colinbdclark/lichen-eurorack-hardware/lichen-breadboard-adaptors/lichen-breadboard-alpha-pot-dual-adaptor/lichen-breadboard-alpha-pot-dual-adaptor.kicad_pcb

## KiCad design lichen-breadboard-adaptors/lichen-breadboard-alpha-pot-dual-adaptor/lichen-breadboard-alpha-pot-dual-adaptor.kicad_pcb (2025-12-30)

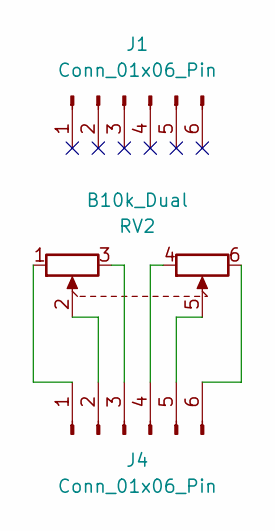
[picture p50: schematic lichen-breadboard-alpha-pot-dual-adaptor.kicad_sch]

Parts:
J1, J4: Conn_01x06_Pin; PinHeader_1x06_P2.54mm_Vertical
RV2: B10k_Dual; Potentiometer_Alpha_RD902F-40-00D_Dual_Vertical; Part Number RD90F-40

Connections:
unnamed: J4.1, RV2.1
unnamed: J4.2, RV2.2
unnamed: J4.3, RV2.3
unnamed: J4.4, RV2.4
unnamed: J4.5, RV2.5
unnamed: J4.6, RV2.6

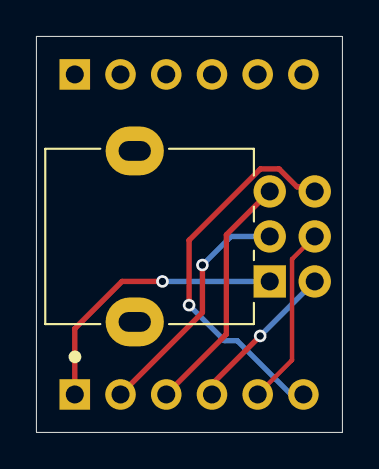
[picture p51: board lichen-breadboard-alpha-pot-dual-adaptor.kicad_pcb from above]

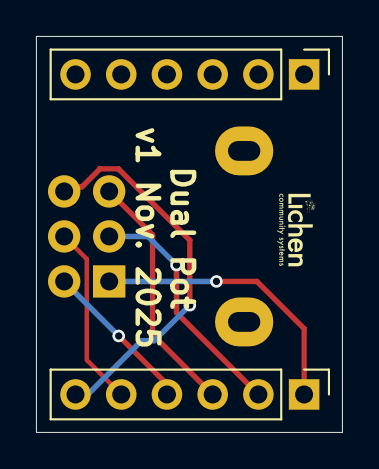
[picture p52: board lichen-breadboard-alpha-pot-dual-adaptor.kicad_pcb from below]

Board: 2 copper layers, 17.0 x 22.0 mm, 3 parts (2 on the bottom side), 6 nets.
