colinbdclark/lichen-eurorack-hardware/lichen-breadboard-adaptors/lichen-breadboard-spdt-switch-adaptor/lichen-breadboard-spdt-switch-adaptor.kicad_pcb

## KiCad design lichen-breadboard-adaptors/lichen-breadboard-spdt-switch-adaptor/lichen-breadboard-spdt-switch-adaptor.kicad_pcb (2025-12-30)

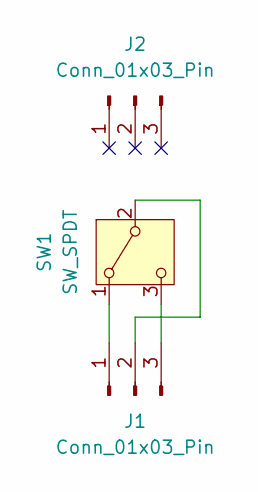
[picture p53: schematic lichen-breadboard-spdt-switch-adaptor.kicad_sch]

Parts:
J1, J2: Conn_01x03_Pin; PinHeader_1x03_P2.54mm_Vertical
SW1: SW_SPDT; Miniature_Switch_SPDT_2.54MM

Connections:
unnamed: J1.1, SW1.1 (A)
unnamed: J1.2, SW1.2 (B)
unnamed: J1.3, SW1.3 (C)

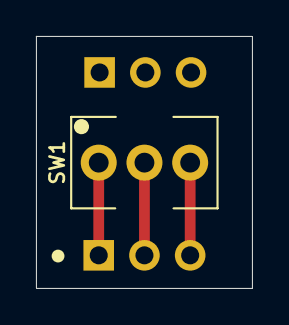
[picture p54: board lichen-breadboard-spdt-switch-adaptor.kicad_pcb from above]

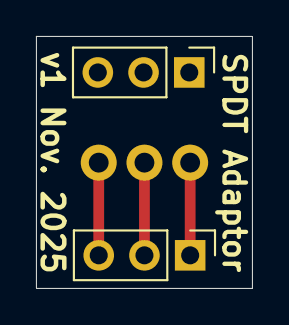
[picture p55: board lichen-breadboard-spdt-switch-adaptor.kicad_pcb from below]

Board: 2 copper layers, 12.0 x 14.0 mm, 3 parts (2 on the bottom side), 3 nets.
