colinbdclark/lichen-eurorack-hardware/lichen-breadboard-adaptors/lichen-breadboard-alpha-pot-single-adaptor/lichen-breadboard-alpha-pot-single-adaptor.kicad_pcb

## KiCad design lichen-breadboard-adaptors/lichen-breadboard-alpha-pot-single-adaptor/lichen-breadboard-alpha-pot-single-adaptor.kicad_pcb (2025-12-30)

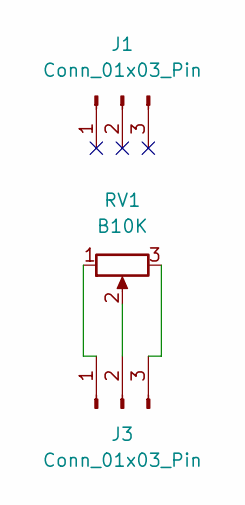
[picture p56: schematic lichen-breadboard-alpha-pot-single-adaptor.kicad_sch]

Parts:
J1, J3: Conn_01x03_Pin; PinHeader_1x03_P2.54mm_Vertical
RV1: B10K; Potentiometer_Alpha_RD901_Eurorack; Part Number RD901F-40

Connections:
unnamed: J3.1, RV1.1
unnamed: J3.2, RV1.2
unnamed: J3.3, RV1.3

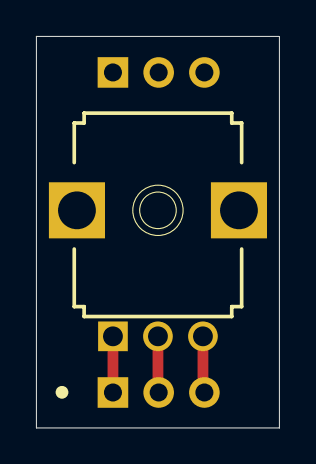
[picture p57: board lichen-breadboard-alpha-pot-single-adaptor.kicad_pcb from above]

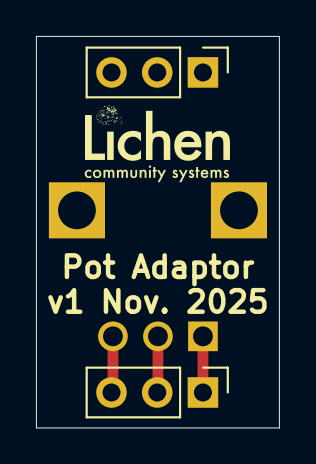
[picture p58: board lichen-breadboard-alpha-pot-single-adaptor.kicad_pcb from below]

Board: 2 copper layers, 13.5 x 21.8 mm, 3 parts (2 on the bottom side), 3 nets.
