colinbdclark/lichen-eurorack-hardware/lichen-four/lichen-four-board/lichen-four-board.kicad_pcb

## KiCad design lichen-four/lichen-four-board/lichen-four-board.kicad_pcb (2025-12-17)

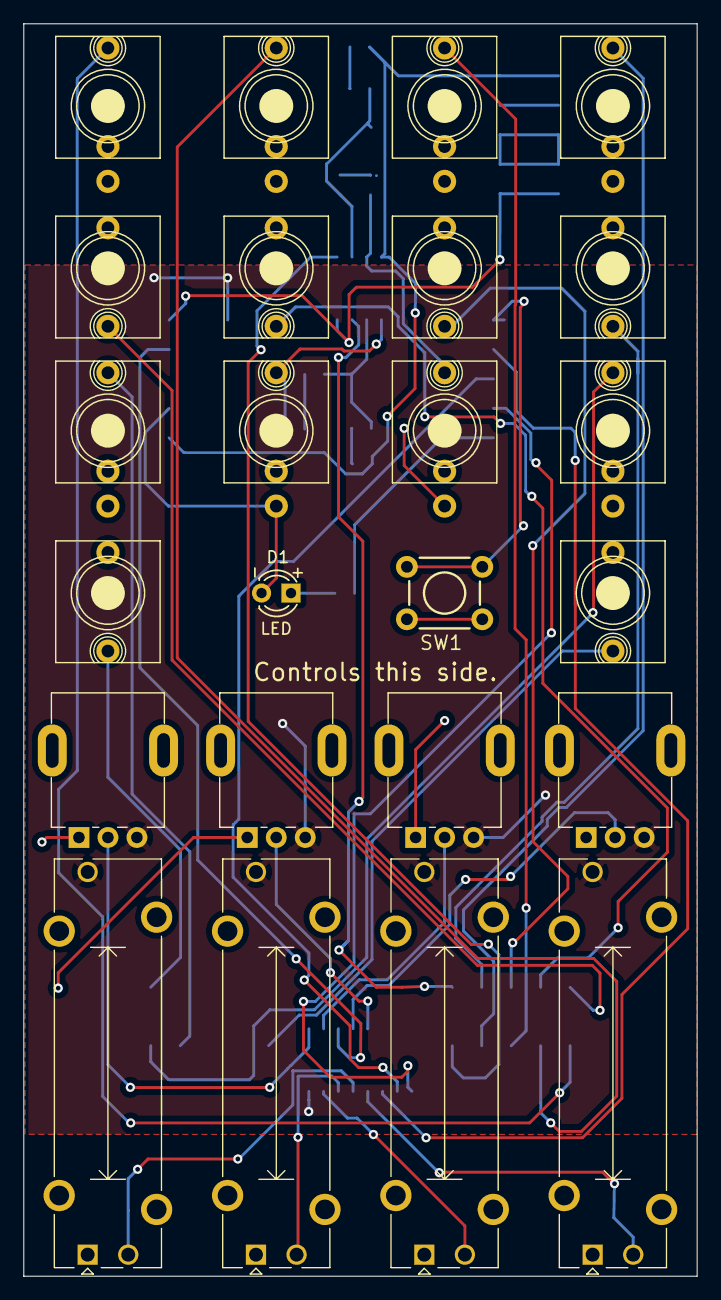
[picture p59: board lichen-four-board.kicad_pcb from above]

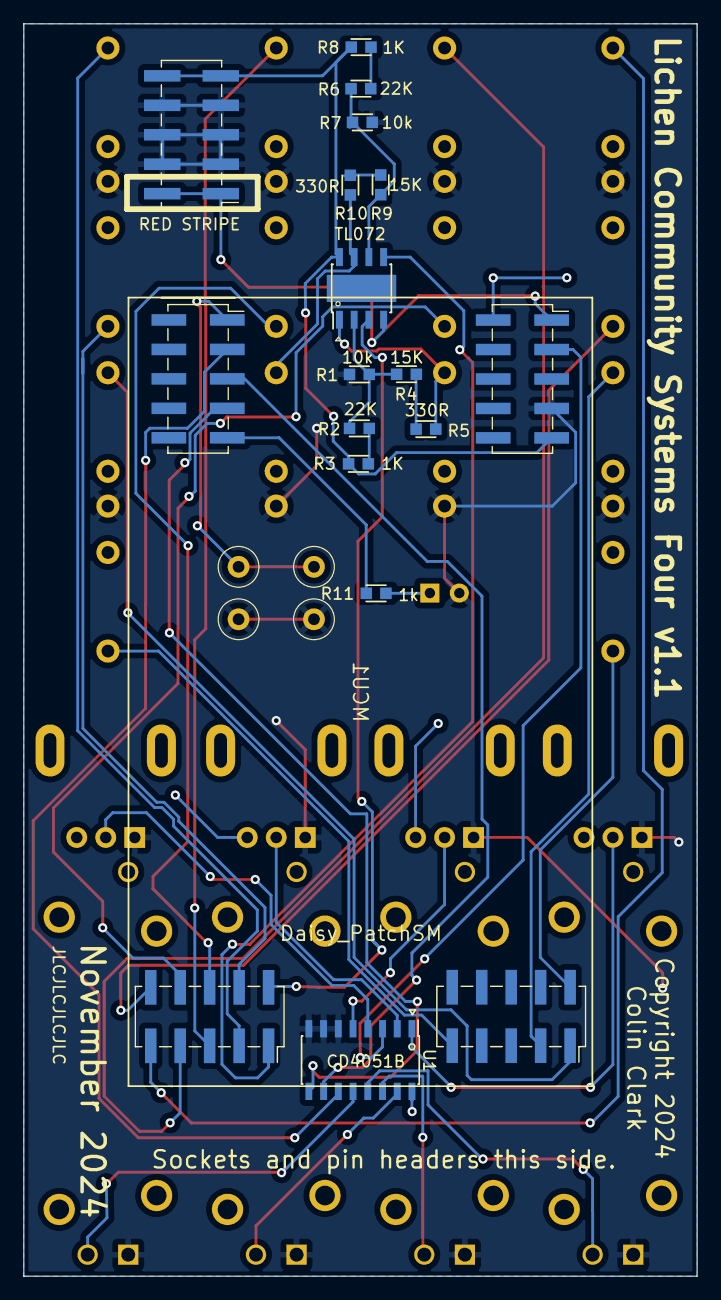
[picture p60: board lichen-four-board.kicad_pcb from below]

Board: 2 copper layers, 58.1 x 108.0 mm, 39 parts (14 on the bottom side), 41 nets.

Parts:
D1: LED; LED_3mm_C1A2_Polarity_Indicator
J1, J2, J3, J4, J9, J10, J11, J12: Eurorack_Mono_Jack; AudioJack_WQP518MA
J5, J6, J7, J8, J13, J14: Eurorack_Mono_Jack; AudioJack_WQP518MA_No_S
MCU1: Daisy_PatchSM; Daisy_Patch_Submodule_SMD
PWR1: Eurorack_Power; PinHeader_2x05_P2.54mm_Vertical_SMD
R1, R6: 10k; R_0603
R2, R7: 22K; R_0603
R3, R8: 1K; R_0603
R4, R9: 15K; R_0603
R5, R10: 330R; R_0603
R11: 1k; R_0603
RV1, RV2, RV3, RV4: R_Potentiometer; Potentiometer_Bourns_PTA2043_Single_Slide
RV5, RV6, RV7, RV8: Eurorack_Pot; Potentiometer_Alpha_R0904N
SW1: TL1105SPF250Q; TL1105SPF250Q_SILK
U1: CD4051B; SOIC-16_3.9x9.9mm_Pitch1.27mm
U2: TL072; SOIC-8-1EP_3.9x4.9mm_Pitch1.27mm_HandSolder

Connections:
+3.3V: MCU1.A10 (+3V3), RV1.3, RV2.3, RV3.3, RV4.3, RV5.3, RV6.3, RV7.3, RV8.3, U1.16 (VDD)
+12V: MCU1.A5 (+12V), PWR1.9 (+12V), PWR1.10 (+12V), R3.2, R8.2, U2.8 (V+)
-12V: MCU1.A1 (-12V), PWR1.1 (-12V), PWR1.2 (-12V), U2.4 (V-)
ADC_MUX: MCU1.A2 (UART_RX), U1.3 (X)
AUDIO_CV_OUT_1: J9.T (Tip), MCU1.B2 (AUDIO_OUT_L)
AUDIO_CV_OUT_2: J12.T (Tip), MCU1.B1 (AUDIO_OUT_R)
BIPOLAR_CV_OUT_1: J10.T (Tip), R5.2, U2.1
BIPOLAR_CV_OUT_2: J11.T (Tip), R10.2, U2.7
CHANNEL_SEL_A: MCU1.D2 (SDMMC_D3), U1.11 (A)
CHANNEL_SEL_B: MCU1.D3 (SDMMC_D2), U1.10 (B)
CHANNEL_SEL_C: MCU1.D4 (SDMMC_D1), U1.9 (C)
CV_JACK_1: J1.T (Tip), MCU1.C5 (CV1)
CV_JACK_2: J2.T (Tip), MCU1.C4 (CV2)
CV_JACK_3: J3.T (Tip), MCU1.C3 (CV3)
CV_JACK_4: J4.T (Tip), MCU1.C2 (CV4)
CV_JACK_5: J5.T (Tip), MCU1.C6 (CV5)
CV_JACK_6: J6.T (Tip), MCU1.C7 (CV6)
CV_JACK_7: J7.T (Tip), MCU1.C8 (CV7)
CV_JACK_8: J8.T (Tip), MCU1.C9 (CV8)
GATE_IN_1: J13.T (Tip), MCU1.B10 (GATE_IN_1)
GATE_OUT_1: J14.T (Tip), MCU1.B5 (GATE_OUT_1)
GND: D1.1 (K), J1.S (Sleeve), J2.S (Sleeve), J3.S (Sleeve), J4.S (Sleeve), J9.S (Sleeve), J10.S (Sleeve), J11.S (Sleeve), J12.S (Sleeve), MCU1.A4 (GND), PWR1.3 (GND), PWR1.4 (GND), PWR1.5 (GND), PWR1.6 (GND), PWR1.7 (GND), PWR1.8 (GND), R1.1, R6.1, RV1.1, RV2.1, RV3.1, RV4.1, RV5.1, RV6.1, RV7.1, RV8.1, SW1.3, SW1.4, U1.6 (INH), U1.7 (VEE), U1.8 (VSS)
GPIO_BUTTON_1: MCU1.D1 (SPI_NSS), SW1.1, SW1.2
GPIO_LED_1: MCU1.D5 (SDMMC_D0), R11.2
unnamed: D1.2 (A), R11.1
unnamed: R2.2, R3.1
unnamed: R4.2, R5.1
unnamed: R7.2, R8.1
unnamed: R9.2, R10.1
unnamed: RV1.2, U1.13 (X0)
unnamed: RV2.2, U1.14 (X1)
unnamed: RV3.2, U1.15 (X2)
unnamed: RV4.2, U1.12 (X3)
unnamed: RV5.2, U1.1 (X4)
unnamed: RV6.2, U1.5 (X5)
unnamed: RV7.2, U1.2 (X6)
unnamed: RV8.2, U1.4 (X7)
unnamed: R1.2, R2.1, R4.1, U2.2 (-)
unnamed: R6.2, R7.1, R9.1, U2.6 (-)
UNIPOLAR_CV_OUT_1: MCU1.C10 (CV_OUT_1), U2.3 (+)
UNIPOLAR_CV_OUT_2: MCU1.C1 (CV_OUT_2), U2.5 (+)
