colinbdclark/lichen-eurorack-hardware/lichen-passive-mutes/lichen-passive-mutes-board/lichen-passive-mutes-board.kicad_pcb

## KiCad design lichen-passive-mutes/lichen-passive-mutes-board/lichen-passive-mutes-board.kicad_pcb (2024-10-25)

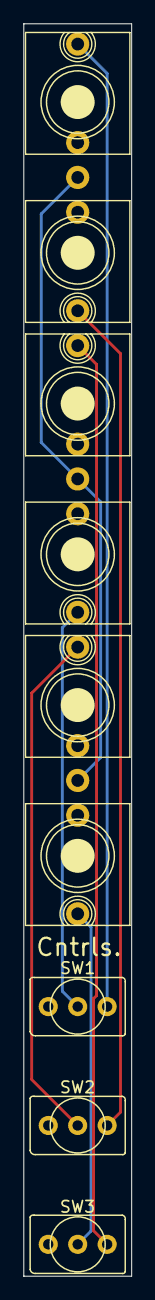
[picture p61: board lichen-passive-mutes-board.kicad_pcb from above]

Board: 2 copper layers, 9.3 x 108.0 mm, 9 parts (0 on the bottom side), 7 nets.

Parts:
J1, J3, J5: Eurorack_Mono_Jack; AudioJack_WQP518MA
J2, J4, J6: Eurorack_Mono_Jack; AudioJack_WQP518MA_No_S
SW1, SW2, SW3: SW_SPDT; Switch_Toggle_SPDT_SubMini

Connections:
GND: J1.S (Sleeve), J3.S (Sleeve), J5.S (Sleeve)
unnamed: J1.T (Tip), SW1.1 (A)
unnamed: J2.T (Tip), SW2.1 (A)
unnamed: J3.T (Tip), SW3.1 (A)
unnamed: J4.T (Tip), SW1.2 (B)
unnamed: J5.T (Tip), SW2.2 (B)
unnamed: J6.T (Tip), SW3.2 (B)
