colinbdclark/lichen-eurorack-hardware/bifocals-filter/lichen-bifocals-control-board/lichen-bifocals-control-board.kicad_pcb

## KiCad design bifocals-filter/lichen-bifocals-control-board/lichen-bifocals-control-board.kicad_pcb (2024-10-25)

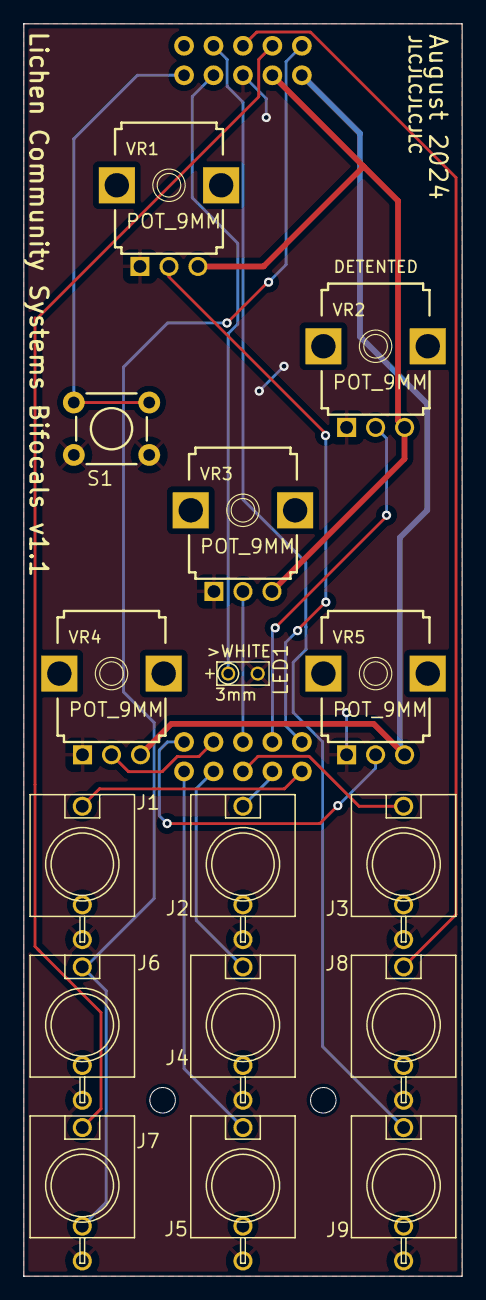
[picture p62: board lichen-bifocals-control-board.kicad_pcb from above]

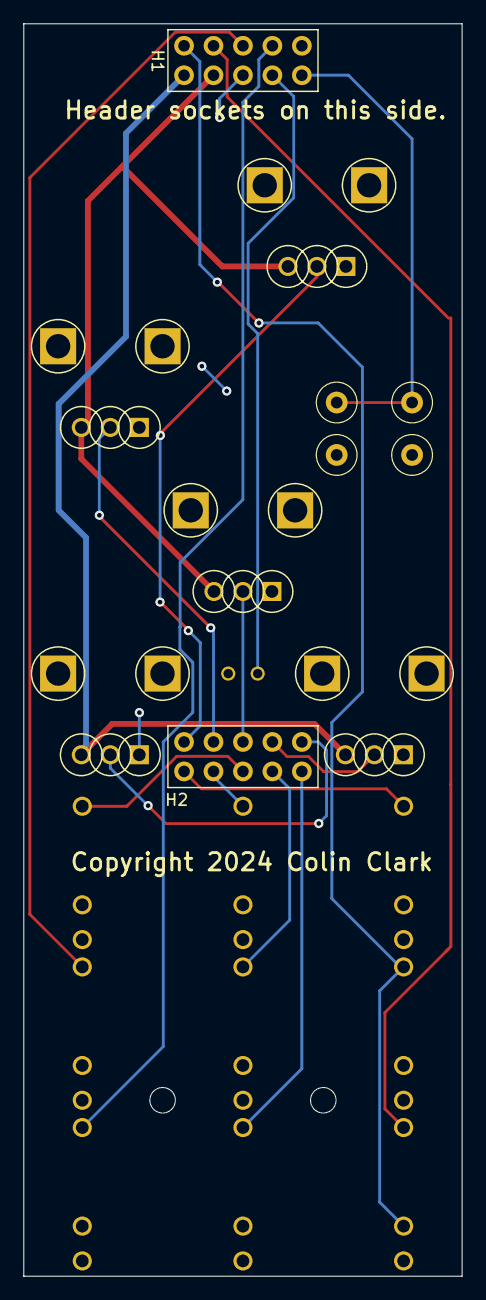
[picture p63: board lichen-bifocals-control-board.kicad_pcb from below]

Board: 2 copper layers, 37.8 x 108.0 mm, 20 parts (2 on the bottom side), 19 nets.

Parts:
H1, H2: PIN_HEADER_2x5; Pins_2x05_2.54mm_TH
J1, J2, J3, J4, J5, J6, J7, J8, J9: EURO_JACK; S_JACK
LED1: LED
MH2, MH2#2: MountingHole_2.2mm_M2
S1: TAC_SWITCH_PTH; TL1105SPF250Q_SILK
VR1, VR2, VR3, VR4, VR5: POT_9MM; 9MM_SNAP-IN_POT_SILK

Connections:
+3.3V: H1.1, VR4.3, VR5.3
+5V: H1.3, VR1.3, VR2.3, VR3.3
AUDIO_IN_L: H1.2, J6.TIP, J7.NORM
AUDIO_IN_R: H1.4, J7.TIP
AUDIO_OUT_L: H1.6, J8.TIP
AUDIO_OUT_R: H1.8, J9.TIP
BUTTON: H1.9, S1.1, S1.2
GND: H1.5, J1.GND, J2.GND, J3.GND, J4.GND, J5.GND, J6.GND, J7.GND, J8.GND, J9.GND, LED1.K (C), S1.3, S1.4, VR1.1, VR2.1, VR3.1, VR4.1, VR5.1
JACK_CV_1: H2.1, J1.TIP
JACK_CV_2: H2.3, J2.TIP
JACK_CV_3: H2.5, J3.TIP
JACK_CV_4: H2.7, J4.TIP
JACK_CV_5: H2.9, J5.TIP
LED_CV_OUT: H1.7, LED1.A
POT_1_CV_6: H2.2, VR1.2
POT_2_CV_7: H2.4, VR2.2
POT_3_CV_8: H2.6, VR3.2
POT_4_CV_9: H2.8, VR4.2
POT_5_CV_10: H2.10, VR5.2
