colinbdclark/lichen-eurorack-hardware/lichen-freddie/lichen-freddie-board/lichen-freddie-board.kicad_pcb

## KiCad design lichen-freddie/lichen-freddie-board/lichen-freddie-board.kicad_pcb (2024-10-25)

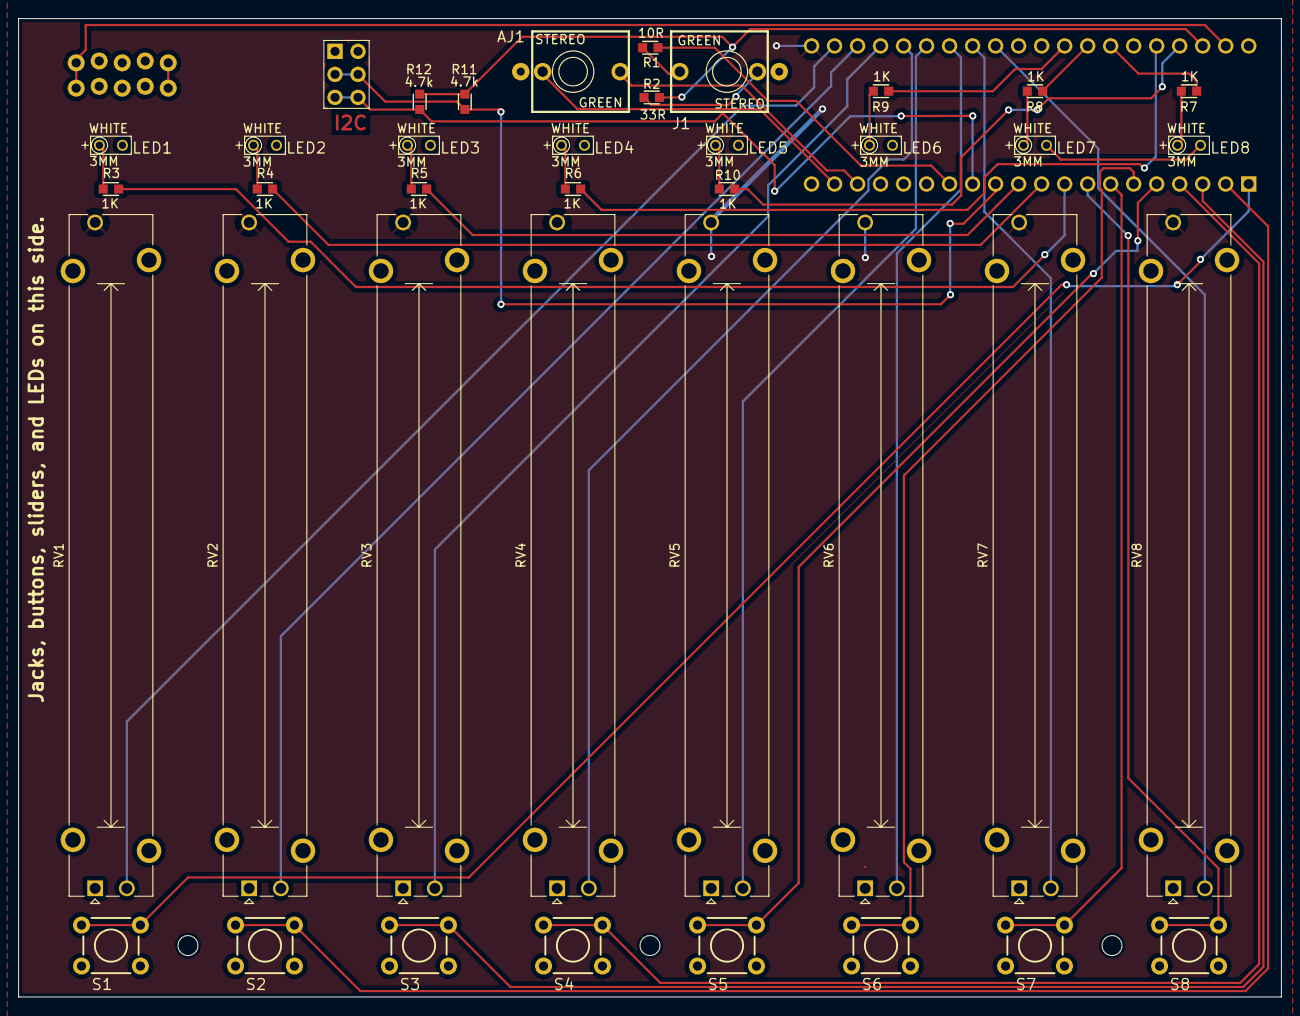
[picture p64: board lichen-freddie-board.kicad_pcb from above]

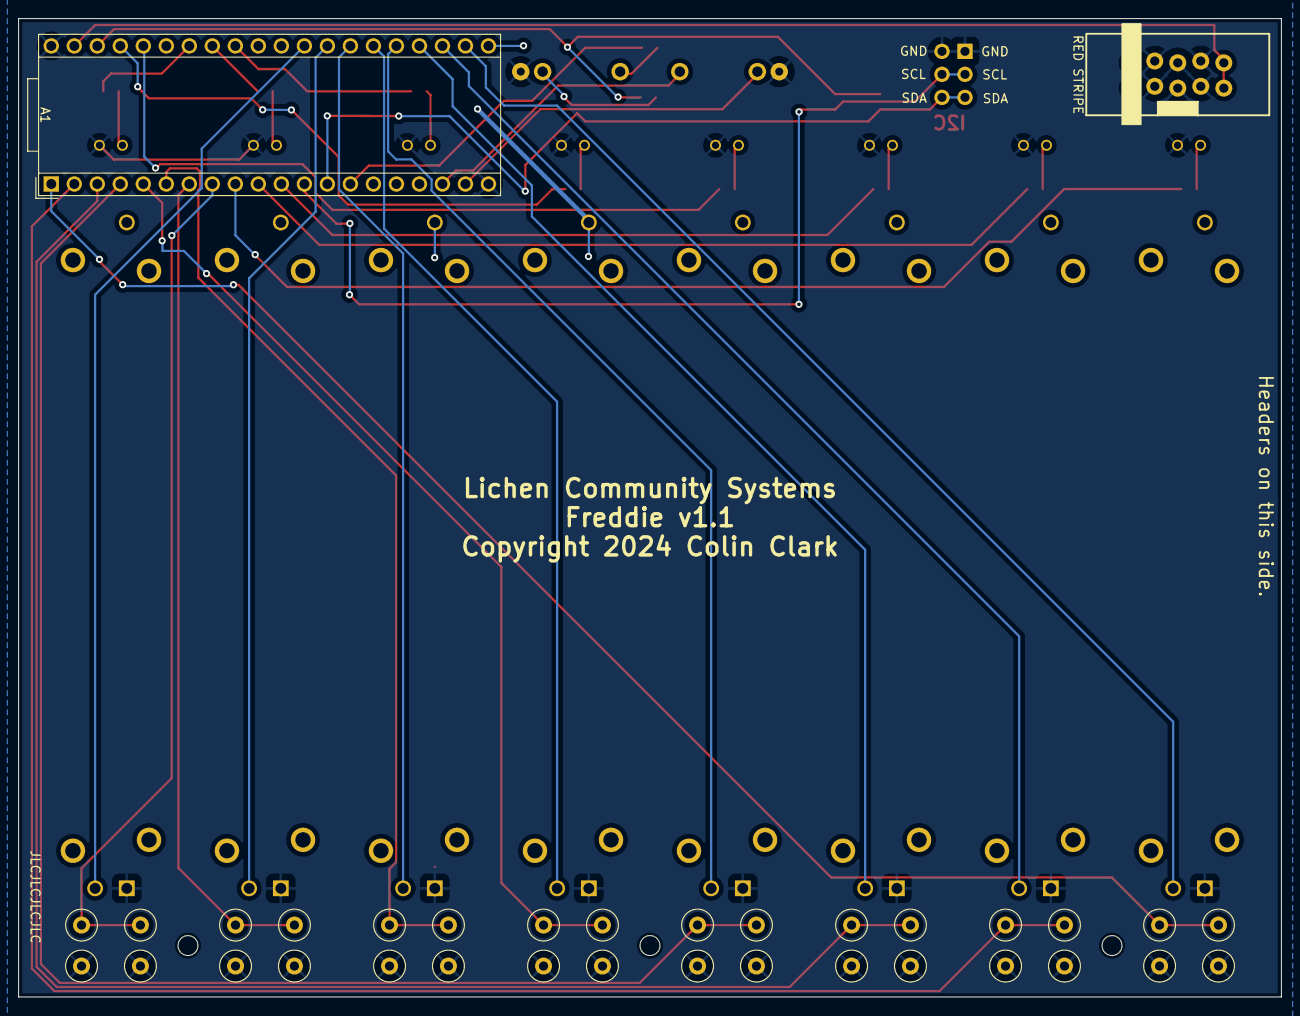
[picture p65: board lichen-freddie-board.kicad_pcb from below]

Board: 2 copper layers, 139.4 x 108.0 mm, 44 parts (2 on the bottom side), 43 nets.

Parts:
A1: Electrosmith_Daisy_Seed_Rev4; Electrosmith_Daisy_Seed
AJ1: 3.5mm_Stereo; EighthInch_Stereo_PJ366ST
H1: Eurorack_Power; Eurorack_Power_2x5_Shrouded_Lock
H2: Conn_02x03; Pins_2x03_2.54mm_TH
J1: 3.5mm_Stereo; EighthInch_Stereo_PJ366ST
LED1, LED2, LED3, LED4, LED5, LED6, LED7, LED8: LED
MH1, MH2, MH3: MountingHole_2.2mm_M2
R1: 10R; R_0603
R2: 33R; R_0603
R3, R4, R5, R6, R7, R8, R9, R10: 1K; R_0603
R11, R12: 4.7k; R_0603
RV1, RV2, RV3, RV4, RV5, RV6, RV7, RV8: R_Potentiometer; Potentiometer_Bourns_PTA6043_Single_Slide_Centered
S1, S2, S3, S4, S5, S6, S7, S8: TAC_SWITCH_PTH; TL1105SPF250Q_SILK

Connections:
3V3D: A1.38 (3V3_D), R2.2, R11.1, R12.2
+3.3VA: A1.21 (3V3_A), RV1.3, RV2.3, RV3.3, RV4.3, RV5.3, RV6.3, RV7.3, RV8.3
+12V: A1.39 (VIN), H1.9 (+12V), H1.10 (+12V)
BUTTON_GPIO_1: A1.1 (USB_ID), S1.1, S1.2
BUTTON_GPIO_2: A1.2 (SD_DATA_3), S2.1, S2.2
BUTTON_GPIO_3: A1.3 (SD_DATA_2), S3.1, S3.2
BUTTON_GPIO_4: A1.4 (SD_DATA_1), S4.1, S4.2
BUTTON_GPIO_5: A1.5 (SD_DATA_0), S5.1, S5.2
BUTTON_GPIO_6: A1.6 (SD_CMD), S6.1, S6.2
BUTTON_GPIO_7: A1.7 (SD_CLK), S7.1, S7.2
BUTTON_GPIO_8: A1.8 (SPI1_CS), S8.1, S8.2
GND: A1.20 (AGND), A1.40 (DGND), AJ1.2 (SHEILD), H1.3 (GND), H1.4 (GND), H1.5 (GND), H1.6 (GND), H1.7 (GND), H1.8 (GND), H2.1 (+12V), H2.2 (+12V), J1.2 (SHEILD), LED1.K (C), LED2.K (C), LED3.K (C), LED4.K (C), LED5.K (C), LED6.K (C), LED7.K (C), LED8.K (C), RV1.1, RV2.1, RV3.1, RV4.1, RV5.1, RV6.1, RV7.1, RV8.1, S1.3, S1.4, S2.3, S2.4, S3.3, S3.4, S4.3, S4.4, S5.3, S5.4, S6.3, S6.4, S7.3, S7.4, S8.3, S8.4
I2C_SCL: A1.12 (I2C1_SCL), H2.3 (GND), H2.4 (GND), R11.2
I2C_SDA: A1.13 (I2C1_SDA), H2.5 (GND), H2.6 (GND), R12.1
LED_GPIO_1: A1.9 (SPI1_SCK), R3.1
LED_GPIO_2: A1.10 (SPI1_POCI), R4.1
LED_GPIO_3: A1.11 (SPI1_PICO), R5.1
LED_GPIO_4: A1.36 (USB_D_-), R6.1
LED_GPIO_5: A1.37 (USB_D_+), R10.2
LED_GPIO_6: A1.32 (SAI2_SD_B), R9.2
LED_GPIO_7: A1.33 (SAI2_SD_A), R8.2
LED_GPIO_8: A1.34 (SAI2_FS), R7.2
unnamed: A1.22 (ADC_0), RV1.2
unnamed: A1.23 (ADC_1), RV2.2
unnamed: A1.24 (ADC_2), RV3.2
unnamed: A1.25 (ADC_3), RV4.2
unnamed: A1.26 (ADC_4), RV5.2
unnamed: A1.27 (ADC_5), RV6.2
unnamed: A1.28 (ADC_6), RV7.2
unnamed: A1.18 (AUDIO_OUT_1), AJ1.1 (SIG)
unnamed: A1.19 (AUDIO_OUT_2), AJ1.3 (SW)
unnamed: A1.29 (DAC_OUT2), RV8.2
unnamed: J1.1 (SIG), R1.1
unnamed: J1.3 (SW), R2.1
unnamed: LED1.A, R3.2
unnamed: LED2.A, R4.2
unnamed: LED3.A, R5.2
unnamed: LED4.A, R6.2
unnamed: LED5.A, R10.1
unnamed: LED6.A, R9.1
unnamed: LED7.A, R8.1
unnamed: LED8.A, R7.1
USART_TX: A1.14 (USART1_TX), R1.2
