colinbdclark/lichen-eurorack-hardware/lichen-medium/lichen-medium-board/lichen-dev-module.kicad_pcb

## KiCad design lichen-medium/lichen-medium-board/lichen-dev-module.kicad_pcb (2024-10-25)

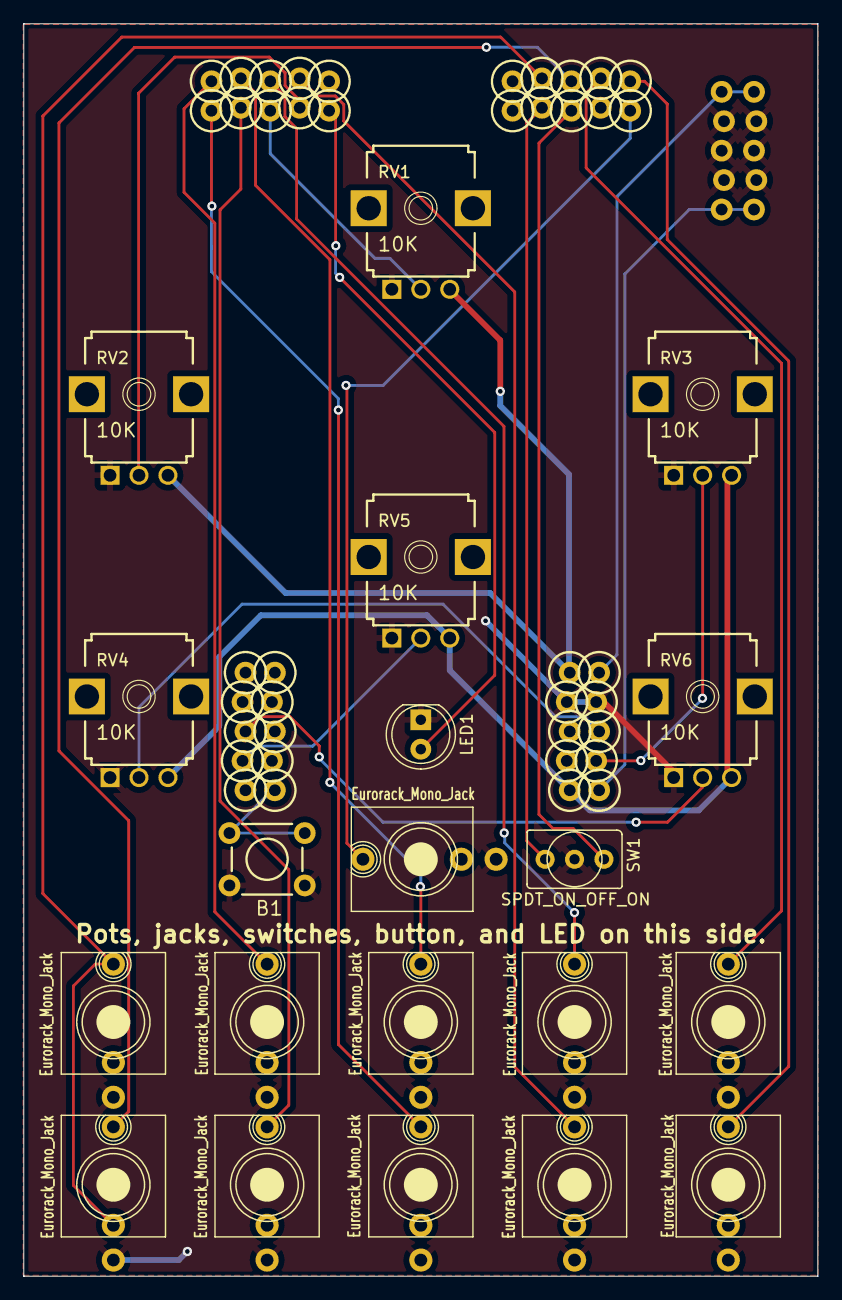
[picture p66: board lichen-dev-module.kicad_pcb from above]

Board: 2 copper layers, 68.6 x 108.2 mm, 22 parts (1 on the bottom side), 26 nets.

Parts:
B1: TAC_SWITCH_PTH; TL1105SPF250Q_SILK
J1, J2, J3, J4, J5, J6, J7, J8, J9, J10, J11: Eurorack_Mono_Jack; AudioJack_WQP518MA
LED1: WHITE; LED_D5.0mm_Clear
MCU1: Daisy Patch Submodule; Daisy_Patch_Submodule
PWR1: Eurorack_Power; Eurorack_Power_2x5_Shrouded_Lock
RV1, RV2, RV3, RV4, RV5, RV6: 10K; 9MM_SNAP-IN_POT_SILK
SW1: SPDT_ON_OFF_ON; Switch_Toggle_SPDT_SubMini

Connections:
+3.3V: MCU1.A10 (+3V3), RV3.3, RV4.3, RV5.3, RV6.3
+5V: MCU1.A6 (+5V), RV1.3, RV2.3
+12V: MCU1.A5 (+12V), PWR1.9 (+12V), PWR1.10 (+12V)
-12V: MCU1.A1 (-12V), PWR1.1 (-12V), PWR1.2 (-12V)
AUDIO_IN_L: J7.T (Tip), J8.TN (Tip_normalize), MCU1.B4 (AUDIO_IN_L)
AUDIO_IN_R: J8.T (Tip), MCU1.B3 (AUDIO_IN_R)
AUDIO_OUT_L: J9.T (Tip), MCU1.B2 (AUDIO_OUT_L)
AUDIO_OUT_R: J10.T (Tip), MCU1.B1 (AUDIO_OUT_R)
BUTTON: B1.1, B1.2, MCU1.D1 (SPI_NSS)
CV_IN_1: J1.T (Tip), MCU1.C5 (CV1)
CV_IN_2: J2.T (Tip), MCU1.C4 (CV2)
CV_IN_3: J3.T (Tip), MCU1.C3 (CV3)
CV_IN_4: J6.T (Tip), MCU1.C2 (CV4)
CV_IN_5: J5.T (Tip), MCU1.C6 (CV5)
CV_IN_6: J4.T (Tip), MCU1.C7 (CV6)
CV_OUT_LED: LED1.2, MCU1.C10 (CV_OUT_1)
GATEIN: J11.T (Tip), MCU1.B10 (GATE_IN_1)
GND: B1.3, B1.4, J1.S (Sleeve), J2.S (Sleeve), J3.S (Sleeve), J4.S (Sleeve), J5.S (Sleeve), J6.S (Sleeve), J7.S (Sleeve), J8.S (Sleeve), J9.S (Sleeve), J10.S (Sleeve), J11.S (Sleeve), LED1.1, MCU1.A4 (GND), MCU1.A7 (GND), PWR1.3 (GND), PWR1.4 (GND), PWR1.5 (GND), PWR1.6 (GND), PWR1.7 (GND), PWR1.8 (GND), RV1.1, RV2.1, RV3.1, RV4.1, RV5.1, RV6.1, SW1.2
POT_CV_1: MCU1.C8 (CV7), RV1.2
POT_CV_2: MCU1.C9 (CV8), RV2.2
POT_CV_3: MCU1.A2 (UART_RX), RV3.2
POT_CV_4: MCU1.A3 (UART_TX), RV4.2
POT_CV_5: MCU1.D9 (SPI_MOSI), RV5.2
POT_CV_6: MCU1.D8 (SPI_MISO), RV6.2
SWITCH_ON_LEFT: MCU1.B7 (I2C1_SCL), SW1.1
SWITCH_ON_RIGHT: MCU1.B8 (I2C1_SDA), SW1.3
