colinbdclark/lichen-eurorack-hardware/bifocals-filter/lichen-bifocals-submodule-power-board/lichen-bifocals-submodule-power-board.kicad_pcb

## KiCad design bifocals-filter/lichen-bifocals-submodule-power-board/lichen-bifocals-submodule-power-board.kicad_pcb (2024-10-25)

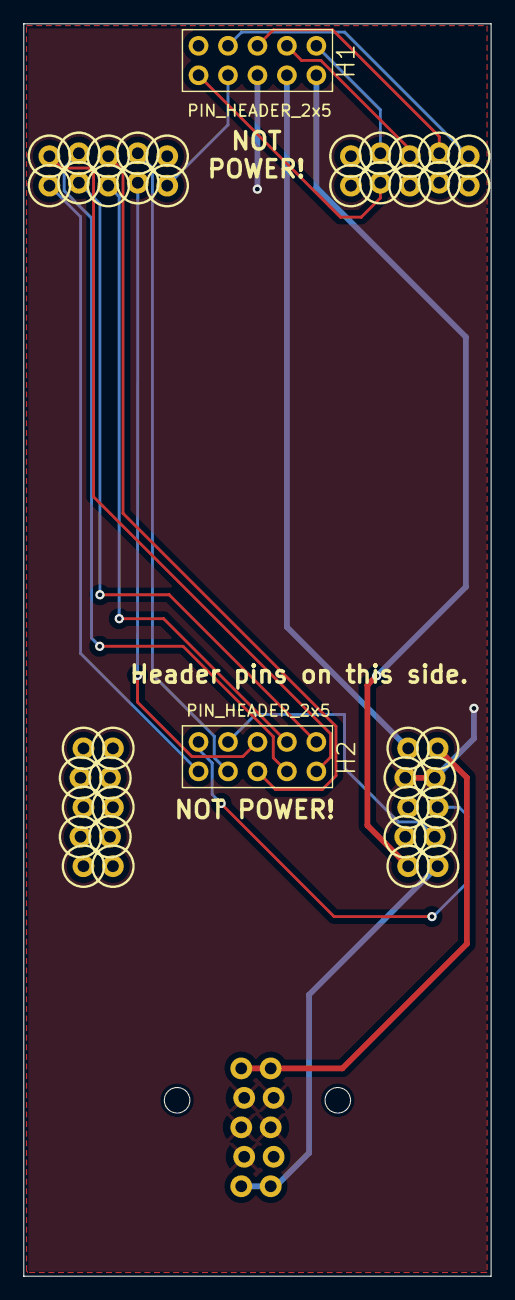
[picture p67: board lichen-bifocals-submodule-power-board.kicad_pcb from above]

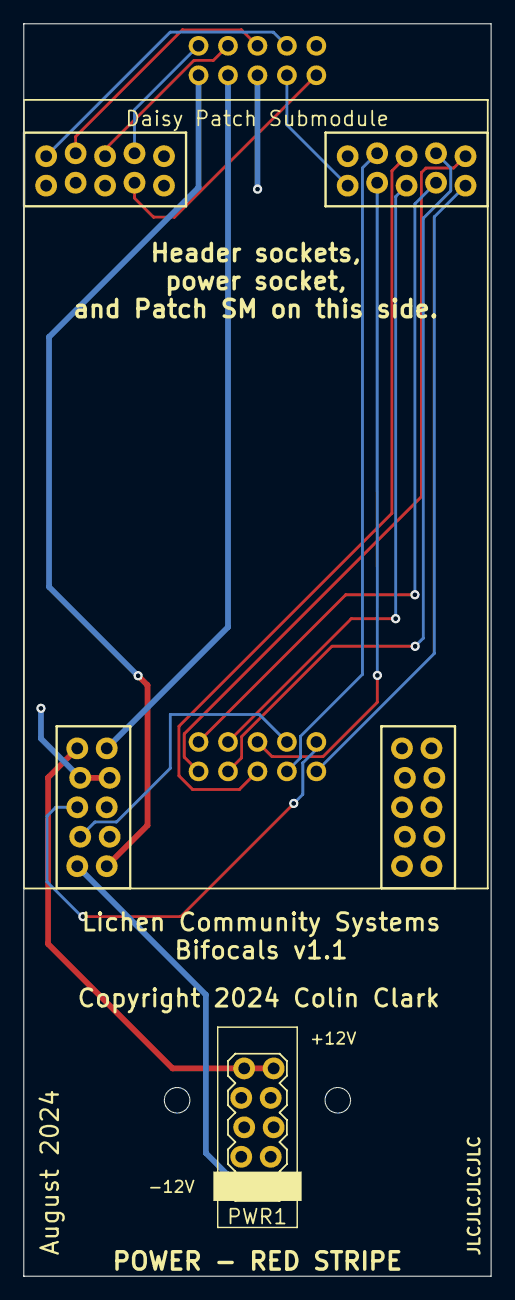
[picture p68: board lichen-bifocals-submodule-power-board.kicad_pcb from below]

Board: 2 copper layers, 40.3 x 108.0 mm, 6 parts (3 on the bottom side), 21 nets.

Parts:
H1, H2: PIN_HEADER_2x5; Pins_2x05_2.54mm_TH
MCU1: Daisy Patch Submodule; Daisy_Patch_Submodule
MH1, MH2: MountingHole_2.2mm_M2
PWR1: EURORACK_POWERSHROUD; EURORACK_POWER_SHROUD_LOCK

Connections:
+3.3V: H1.1, MCU1.A10 (+3V3)
+5V: H1.3, MCU1.A6 (+5V)
+12V: MCU1.A5 (+12V), PWR1.POS1, PWR1.POS2
-12V: MCU1.A1 (-12V), PWR1.NEG1, PWR1.NEG2
AUDIO_IN_L: H1.2, MCU1.B4 (AUDIO_IN_L)
AUDIO_IN_R: H1.4, MCU1.B3 (AUDIO_IN_R)
AUDIO_OUT_L: H1.6, MCU1.B2 (AUDIO_OUT_L)
AUDIO_OUT_R: H1.8, MCU1.B1 (AUDIO_OUT_R)
BUTTON: H1.9, MCU1.B7 (I2C1_SCL)
GND: H1.5, MCU1.A4 (GND), MCU1.A7 (GND), PWR1.GND1 (GND), PWR1.GND2 (GND), PWR1.GND3 (GND), PWR1.GND4 (GND), PWR1.GND5 (GND)
JACK_CV_1: H2.1, MCU1.C5 (CV1)
JACK_CV_2: H2.3, MCU1.C4 (CV2)
JACK_CV_3: H2.5, MCU1.C3 (CV3)
JACK_CV_4: H2.7, MCU1.C2 (CV4)
JACK_CV_5: H2.9, MCU1.C6 (CV5)
LED_CV_OUT: H1.7, MCU1.C10 (CV_OUT_1)
POT_1_CV_6: H2.2, MCU1.C7 (CV6)
POT_2_CV_7: H2.4, MCU1.C8 (CV7)
POT_3_CV_8: H2.6, MCU1.C9 (CV8)
POT_4_CV_9: H2.8, MCU1.A2 (UART_RX)
POT_5_CV_10: H2.10, MCU1.A3 (UART_TX)
