colinbdclark/lichen-eurorack-hardware/simple-patchsm-module/simplest-patchsm-module/simplest-patchsm-module.kicad_pcb

## KiCad design simple-patchsm-module/simplest-patchsm-module/simplest-patchsm-module.kicad_pcb (2024-05-10)

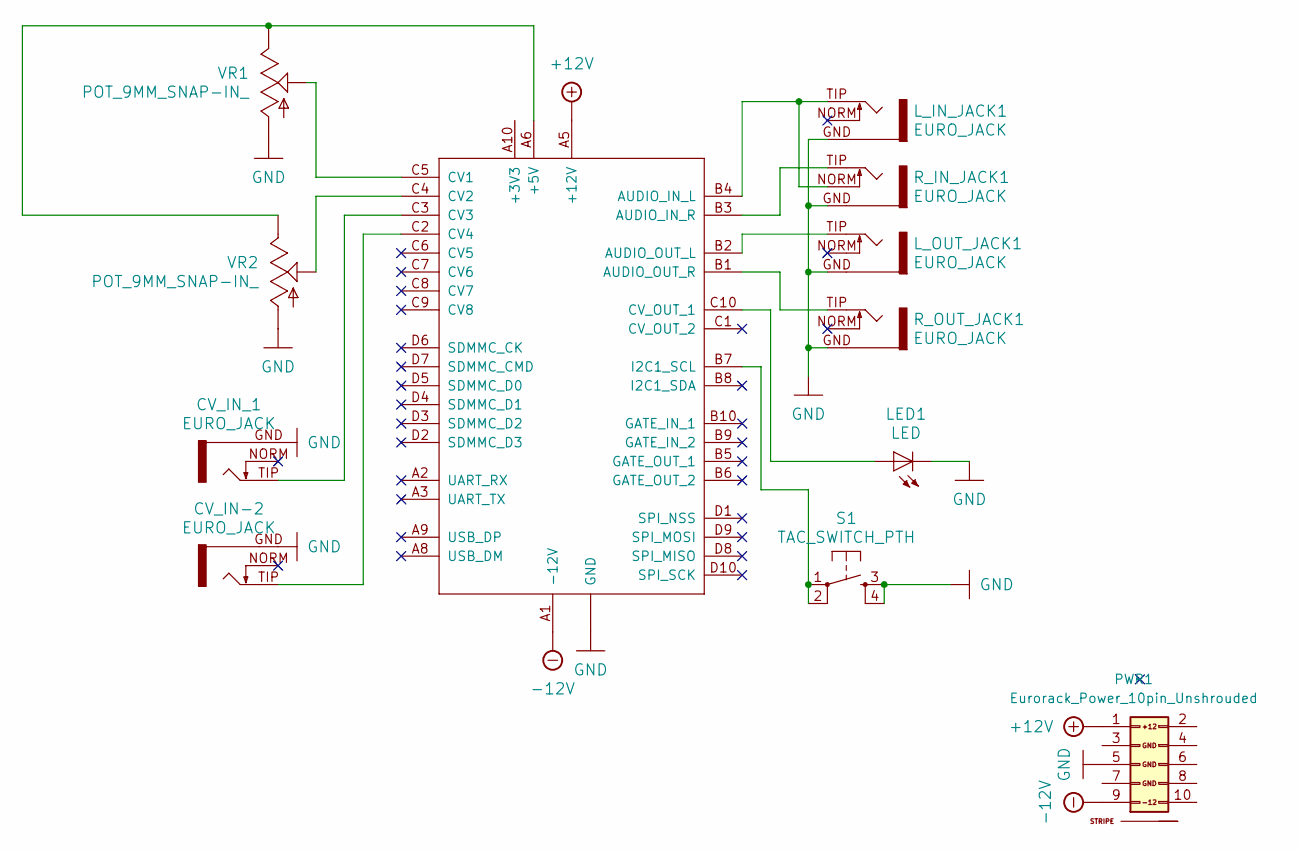
[picture p69: schematic simplest-patchsm-module.kicad_sch, Simplest Patch SM Module]

Parts:
CV_IN-2: EURO_JACK; S_JACK
CV_IN_1: EURO_JACK; S_JACK
LED1: LED
L_IN_JACK1: EURO_JACK; S_JACK
L_OUT_JACK1: EURO_JACK; S_JACK
PATCH_SM1: ES_DAISY_PATCH_SM_REV1
PWR1: Eurorack_Power_10pin_Unshrouded; Pins_2x05_2.54mm_TH_Europower; Part Number 1-1002FBV0T
R_IN_JACK1: EURO_JACK; S_JACK
R_OUT_JACK1: EURO_JACK; S_JACK
S1: TAC_SWITCH_PTH; TL1105SPF250Q_SILK
VR1, VR2: POT_9MM_SNAP-IN_; 9MM_SNAP-IN_POT_SILK

Connections:
+12V: PATCH_SM1.A5 (+12V), PWR1.1 (+12V)
-12V: PATCH_SM1.A1 (-12V), PWR1.9 (-12V)
GND: CV_IN-2.GND, CV_IN_1.GND, LED1.K (C), L_IN_JACK1.GND, L_OUT_JACK1.GND, PATCH_SM1.A4 (GND), PATCH_SM1.A7 (GND), PWR1.5 (GND), R_IN_JACK1.GND, R_OUT_JACK1.GND, S1.3, S1.4, VR1.1, VR2.1
unnamed: PATCH_SM1.A6 (+5V), VR1.3, VR2.3
unnamed: L_IN_JACK1.TIP, PATCH_SM1.B4 (AUDIO_IN_L), R_IN_JACK1.NORM
unnamed: PATCH_SM1.B3 (AUDIO_IN_R), R_IN_JACK1.TIP
unnamed: L_OUT_JACK1.TIP, PATCH_SM1.B2 (AUDIO_OUT_L)
unnamed: PATCH_SM1.B1 (AUDIO_OUT_R), R_OUT_JACK1.TIP
unnamed: PATCH_SM1.C5 (CV1), VR1.2
unnamed: PATCH_SM1.C4 (CV2), VR2.2
unnamed: CV_IN_1.TIP, PATCH_SM1.C3 (CV3)
unnamed: CV_IN-2.TIP, PATCH_SM1.C2 (CV4)
unnamed: LED1.A, PATCH_SM1.C10 (CV_OUT_1)
unnamed: PATCH_SM1.B7 (I2C1_SCL), S1.1, S1.2

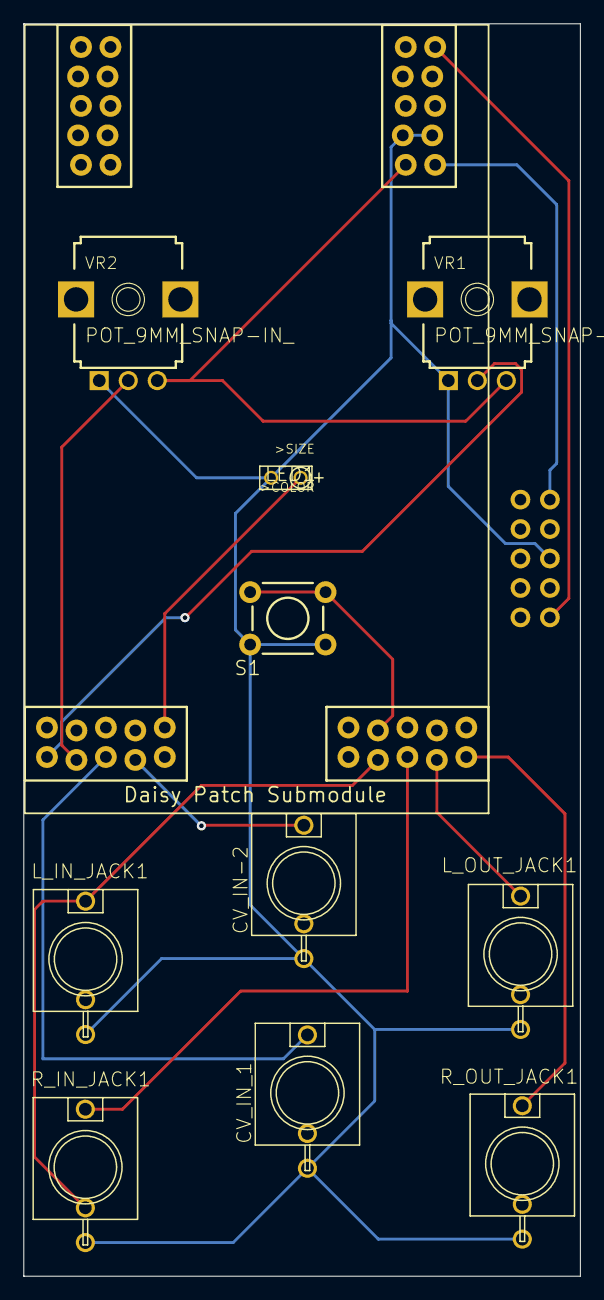
[picture p70: board simplest-patchsm-module.kicad_pcb from above]

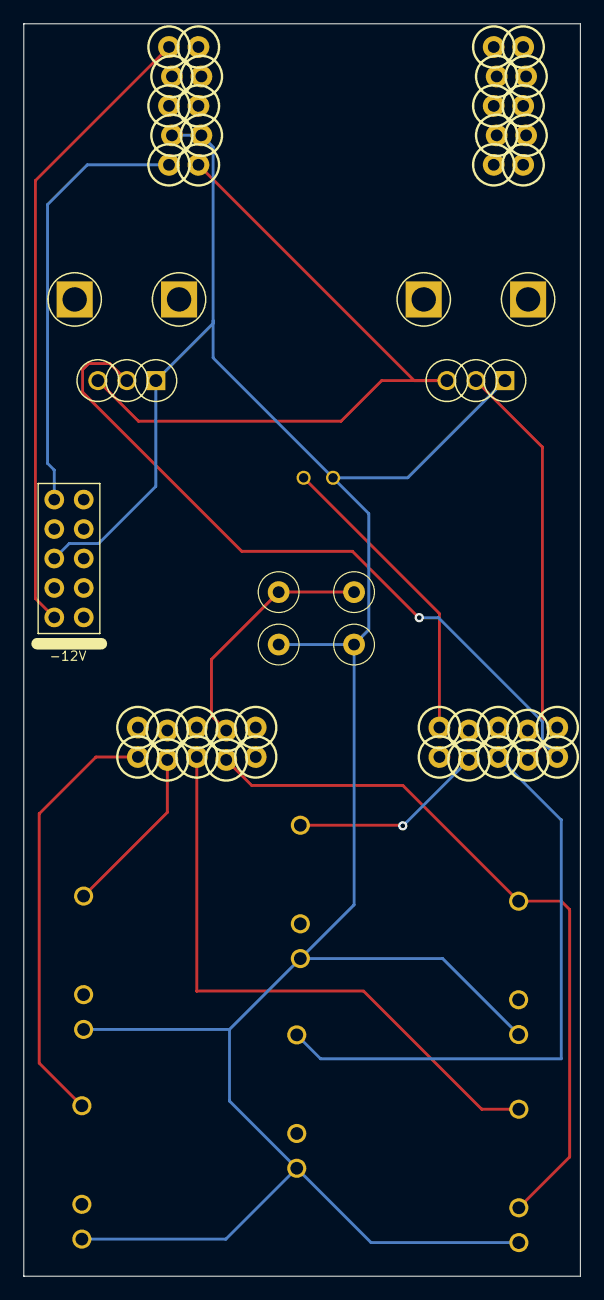
[picture p71: board simplest-patchsm-module.kicad_pcb from below]

Board: 2 copper layers, 48.0 x 108.0 mm, 12 parts (2 on the bottom side), 14 nets.
