colinbdclark/lichen-eurorack-hardware/Lichen_Design_Blocks.kicad_blocks/3V3 Buck-Boost Regulator TPS63031.kicad_block/3V3 Buck-Boost Regulator TPS63031.kicad_sch

## KiCad design Lichen_Design_Blocks.kicad_blocks/3V3 Buck-Boost Regulator TPS63031.kicad_block/3V3 Buck-Boost Regulator TPS63031.kicad_sch (2026-03-04)

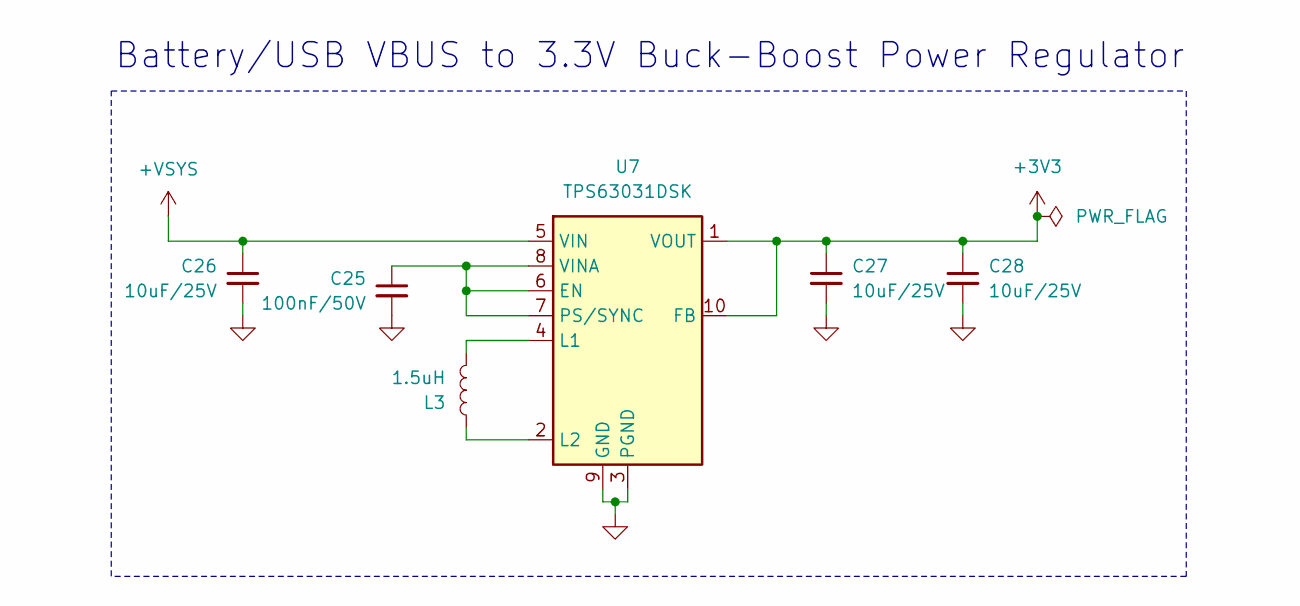
[picture p72: schematic 3V3 Buck-Boost Regulator TPS63031.kicad_sch]

Parts:
C25: 100nF_0603_50V; C_0603; Part Number CC0603KRX7R9BB104; LCSC C14663
C26, C27, C28: 10uF_0603_25V; C_0603; Part Number GRM188R61E106KA73D; LCSC C344022
L3: 1.5uH; LQH3NPN100MMEL; Part Number LQH3NPN1R5MJRL; LCSC C701165
U7: TPS63031DSK; WSON-10-1EP_2.5x2.5mm_P0.5mm_EP1.2x2mm; Part Number TPS63031DSKR

Connections:
+3V3: C27.1, C28.1, U7.1 (VOUT), U7.10 (FB)
+VSYS: C26.1, U7.5 (VIN)
GND: C25.2, C26.2, C27.2, C28.2, U7.3 (PGND), U7.9 (GND), U7.11 (PGND)
unnamed: C25.1, U7.6 (EN), U7.7 (PS/SYNC), U7.8 (VINA)
unnamed: L3.1, U7.4 (L1)
unnamed: L3.2, U7.2 (L2)

Notes on the sheet:
Battery/USB VBUS to 3.3V Buck-Boost Power Regulator
