colinbdclark/lichen-eurorack-hardware/Lichen_Design_Blocks.kicad_blocks/5V Fixed Boost Regulator.kicad_block/5V Fixed Boost Regulator.kicad_sch

## KiCad design Lichen_Design_Blocks.kicad_blocks/5V Fixed Boost Regulator.kicad_block/5V Fixed Boost Regulator.kicad_sch (2026-01-12)

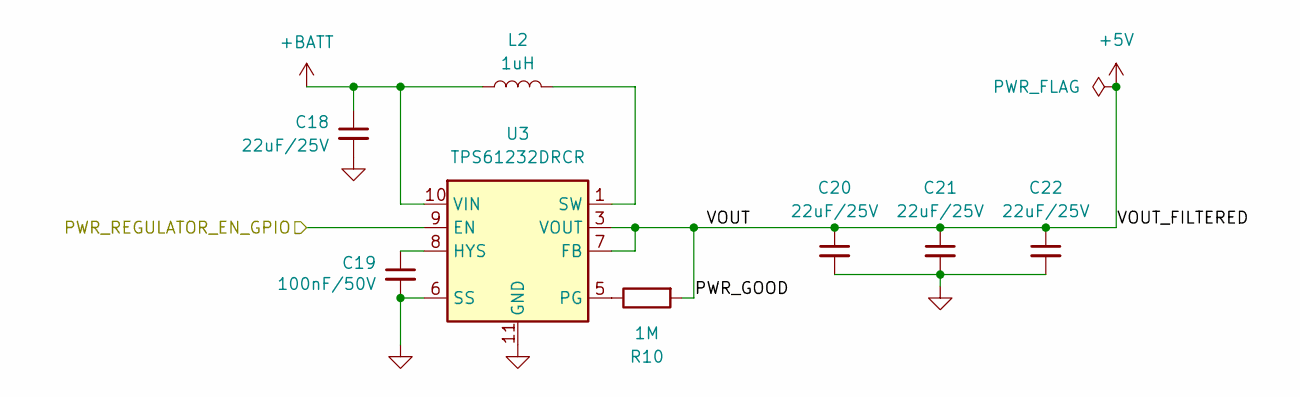
[picture p73: schematic 5V Fixed Boost Regulator.kicad_sch]

Parts:
C18, C20, C21, C22: 22uF; C_0805; Part Number CL21A226MAQNNNE; LCSC C45783
C19: 100nF; C_0603; Part Number CC0603KRX7R9BB104; LCSC C14663
L2: 1uH; L_Coilcraft_XxL4040; Part Number XFL4020-102MEC; LCSC C5355380
R10: 1M; R_0603; Part Number 0603WAF1004T5E; LCSC C22935
U3: TPS61232DRCR; Texas_S-PVSON-N10_ThermalVias; Part Number TPS61232DRCR; LCSC C544315

Connections:
+5V: C20.1, C21.1, C22.1, R10.2, U3.3 (VOUT), U3.4 (VOUT), U3.7 (FB)
+BATT: C18.1, L2.1, U3.10 (VIN)
GND: C18.2, C19.2, C20.2, C21.2, C22.2, U3.6 (SS), U3.11 (GND)
unnamed: C19.1, U3.8 (HYS)
unnamed: L2.2, U3.1 (SW), U3.2 (SW)
unnamed: R10.1, U3.5 (PG)
PWR_REGULATOR_EN_GPIO: U3.9 (EN)
