colinbdclark/lichen-eurorack-hardware/Lichen_Design_Blocks.kicad_blocks/Basic 5V to 3.3V Regulator.kicad_block/Basic 5V to 3.3V Regulator.kicad_sch

## KiCad design Lichen_Design_Blocks.kicad_blocks/Basic 5V to 3.3V Regulator.kicad_block/Basic 5V to 3.3V Regulator.kicad_sch (2025-12-30)

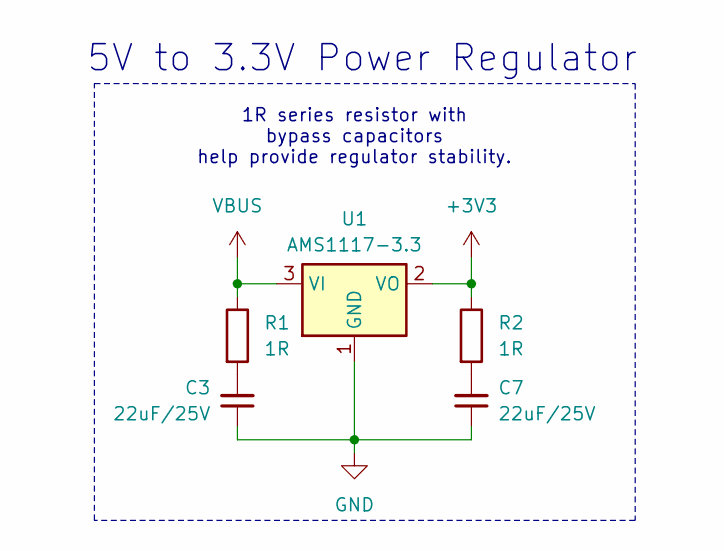
[picture p74: schematic Basic 5V to 3.3V Regulator.kicad_sch]

Parts:
C3, C7: 22uF_0805_25V; C_0805; Part Number CL21A226MAQNNNE; LCSC C45783
R1: 1R; R_0603; Part Number 0603WAF100KT5E; LCSC C22936
R2: 100R_0603; R_0603; Part Number 0603WAF100KT5E; LCSC C22936
U1: AMS1117-3.3; SOT-223-3_TabPin2; Part Number AMS1117-3.3; LCSC C6186

Connections:
+3V3: R2.1, U1.2 (VO)
GND: C3.1, C7.1, U1.1 (GND)
unnamed: C3.2, R1.2
unnamed: C7.2, R2.2
VBUS: R1.1, U1.3 (VI)

Notes on the sheet:
1R series resistor with bypass capacitors help provide regulator stability.
5V to 3.3V Power Regulator
