colinbdclark/lichen-eurorack-hardware/Lichen_Design_Blocks.kicad_blocks/Basic 12V to 5V Regulator.kicad_block/Basic 12V to 5V Regulator.kicad_sch

## KiCad design Lichen_Design_Blocks.kicad_blocks/Basic 12V to 5V Regulator.kicad_block/Basic 12V to 5V Regulator.kicad_sch (2025-12-17)

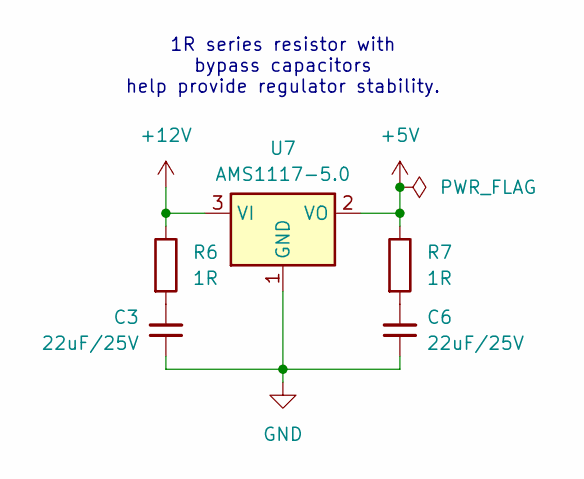
[picture p75: schematic Basic 12V to 5V Regulator.kicad_sch]

Parts:
C3, C6: 22uF_0805_25V; C_0805; Part Number CL21A226MAQNNNE; LCSC C45783
R6: 1R; R_0603; Part Number 0603WAF100KT5E; LCSC C22936
R7: 100R_0603; R_0603; Part Number 0603WAF100KT5E; LCSC C22936
U7: AMS1117-5.0; SOT-223-3_TabPin2; Part Number AMS1117-5.0; LCSC C6187

Connections:
+5V: R7.1, U7.2 (VO)
+12V: R6.1, U7.3 (VI)
GND: C3.1, C6.1, U7.1 (GND)
unnamed: C3.2, R6.2
unnamed: C6.2, R7.2

Notes on the sheet:
1R series resistor with bypass capacitors help provide regulator stability.
