colinbdclark/lichen-eurorack-hardware/Lichen_Design_Blocks.kicad_blocks/Basic Analog Eurorack Power.kicad_block/Basic Analog Eurorack Power.kicad_sch

## KiCad design Lichen_Design_Blocks.kicad_blocks/Basic Analog Eurorack Power.kicad_block/Basic Analog Eurorack Power.kicad_sch (2025-12-17)

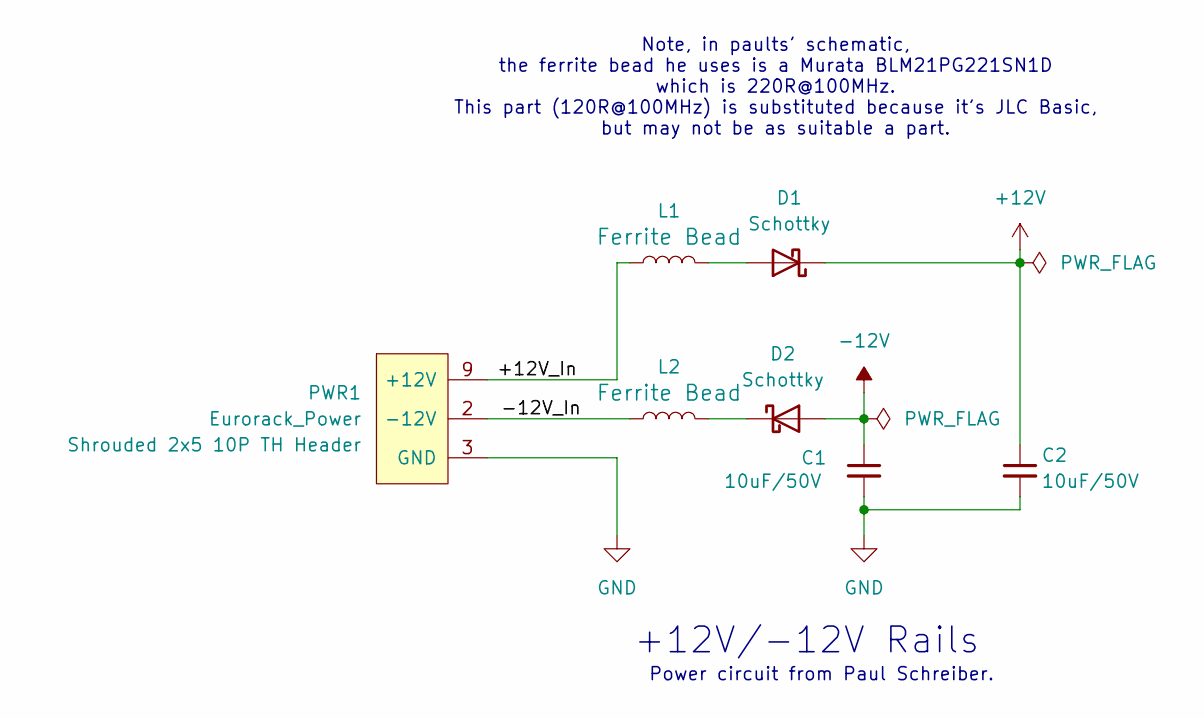
[picture p76: schematic Basic Analog Eurorack Power.kicad_sch]

Parts:
C1, C2: 10uF_0805_25V; C_0805; Part Number GRM21BR61H106KE43L; LCSC C440198
D1: Schottky; D_SMB_Handsoldering; Part Number STPS1L30U; JLCPCB ID C222239
D2: Schottky; D_SMB_Handsoldering; Part Number STPS1L30U; LCSC C222239
L1, L2: FerriteBead_0603_2A; R_0603; Part Number BLM18PG121SN1D; LCSC C14709
PWR1: Eurorack_Power; Eurorack_Power_Shrouded_TH_Staggered_Small

Connections:
+12V: C2.1, D1.1 (K)
+12V_In: L1.1, PWR1.9 (+12V), PWR1.10 (+12V)
-12V: C1.1, D2.2 (A)
-12V_In: L2.1, PWR1.1 (-12V), PWR1.2 (-12V)
GND: C1.2, C2.2, PWR1.3 (GND), PWR1.4 (GND), PWR1.5 (GND), PWR1.6 (GND), PWR1.7 (GND), PWR1.8 (GND)
unnamed: D1.2 (A), L1.2
unnamed: D2.1 (K), L2.2

Notes on the sheet:
Note, in paults' schematic, the ferrite bead he uses is a Murata BLM21PG221SN1D which is 220R@100MHz. This part (120R@100MHz) is substituted because it's JLC Basic, but may not be as suitable a part.
Power circuit from Paul Schreiber.
+12V/-12V Rails
