colinbdclark/lichen-eurorack-hardware/Lichen_Design_Blocks.kicad_blocks/Buffered Input.kicad_block/Buffered Input.kicad_sch

## KiCad design Lichen_Design_Blocks.kicad_blocks/Buffered Input.kicad_block/Buffered Input.kicad_sch (2025-12-17)

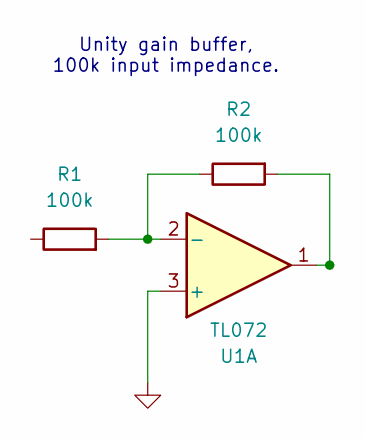
[picture p77: schematic Buffered Input.kicad_sch]

Parts:
R1, R2: 100k; R_0603; Part Number 0603WAF1003T5E; JLCPCB ID C25803
U1: TL072; SOIC-8_3.9x4.9mm_P1.27mm; Part Number TL072CDT; LCSC C6961

Connections:
GND: U1.3 (+)
unnamed: R1.2, R2.1, U1.2 (-)
unnamed: R2.2, U1.1

Notes on the sheet:
Unity gain buffer, 100k input impedance.
