colinbdclark/lichen-eurorack-hardware/Lichen_Design_Blocks.kicad_blocks/Buffered Output.kicad_block/Buffered Output.kicad_sch

## KiCad design Lichen_Design_Blocks.kicad_blocks/Buffered Output.kicad_block/Buffered Output.kicad_sch (2025-12-17)

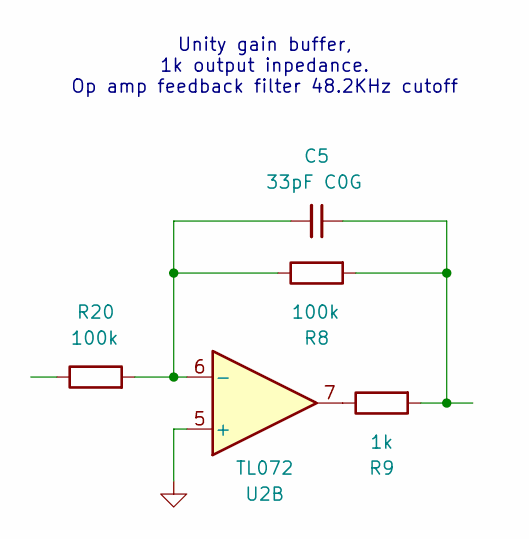
[picture p78: schematic Buffered Output.kicad_sch]

Parts:
C5: 33pF C0G; C_0603; Part Number CL10C330JB8NNNC; LCSC C1663
R8, R20: 10k_0603; R_0603; Part Number 0603WAF1003T5E; JLCPCB ID C25803
R9: 10k_0603; R_0603; Part Number 0603WAF1001T5E; JLCPCB ID C25804
U2: TL072; SOIC-8_3.9x4.9mm_P1.27mm; Part Number TL072CDT; LCSC C6961

Connections:
GND: U2.5 (+)
unnamed: C5.1, R8.2, R9.2
unnamed: C5.2, R8.1, R20.2, U2.6 (-)
unnamed: R9.1, U2.7

Notes on the sheet:
Unity gain buffer, 1k output inpedance. Op amp feedback filter 48.2KHz cutoff
