colinbdclark/lichen-eurorack-hardware/Lichen_Design_Blocks.kicad_blocks/Eurorack Power - All JLC Basic.kicad_block/Eurorack Power - All JLC Basic.kicad_sch

## KiCad design Lichen_Design_Blocks.kicad_blocks/Eurorack Power - All JLC Basic.kicad_block/Eurorack Power - All JLC Basic.kicad_sch (2026-03-17)

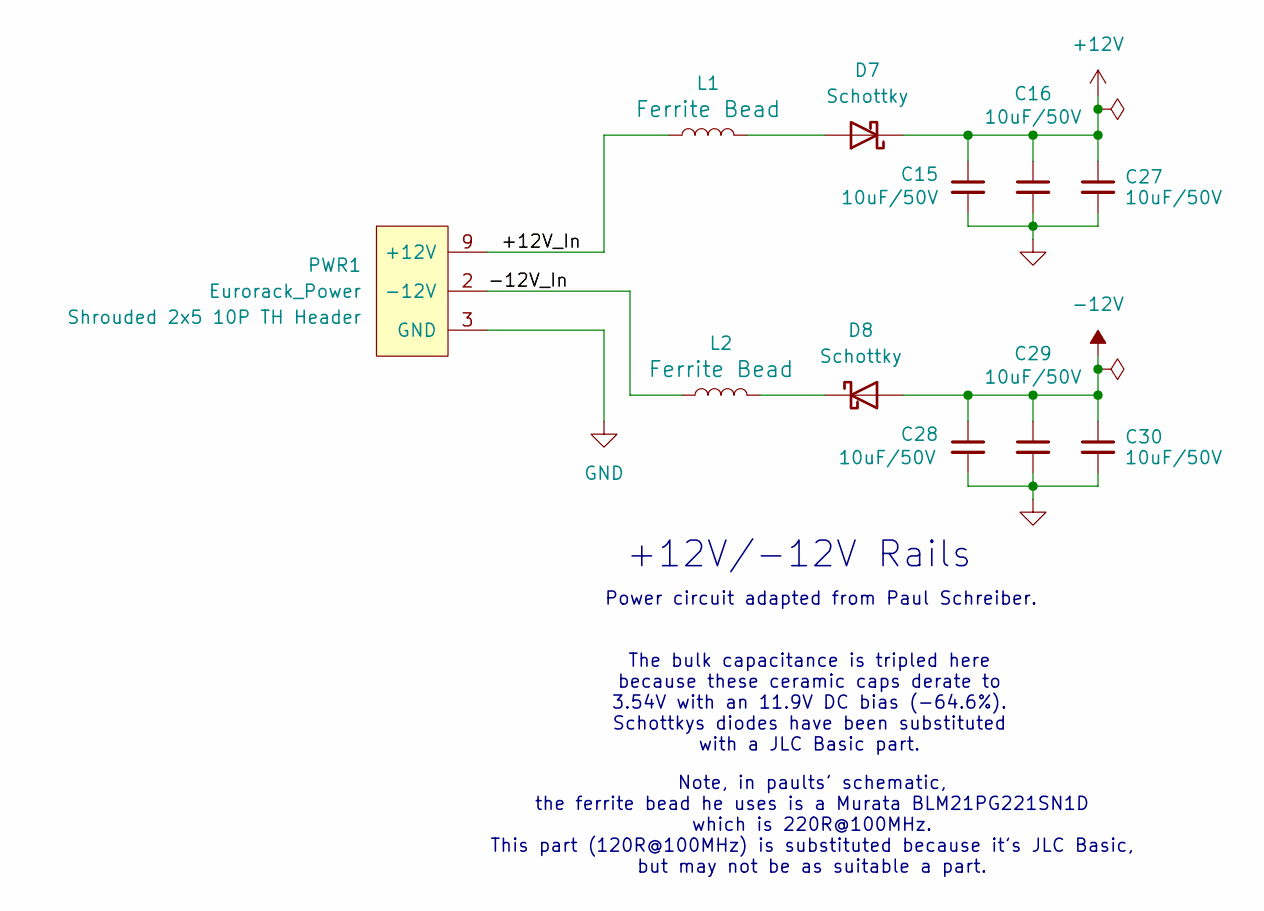
[picture p79: schematic Eurorack Power - All JLC Basic.kicad_sch]

Parts:
C15, C16, C27, C28, C29, C30: 10uF; C_1206_3216Metric; Part Number CL31A106KBHNNNE; LCSC C13585
D7, D8: Schottky; D_SMA_Handsoldering; Part Number SS34; LCSC C8678
L1, L2: FerriteBead_0603_2A; R_0603; Part Number BLM18PG121SN1D; LCSC C14709
PWR1: Eurorack_Power; Eurorack_Power_Shrouded_TH_Staggered_Small

Connections:
+12V: C15.1, C16.1, C27.1, D7.1 (K)
+12V_In: L1.1, PWR1.9 (+12V), PWR1.10 (+12V)
-12V: C28.1, C29.1, C30.1, D8.2 (A)
-12V_In: L2.1, PWR1.1 (-12V), PWR1.2 (-12V)
GND: C15.2, C16.2, C27.2, C28.2, C29.2, C30.2, PWR1.3 (GND), PWR1.4 (GND), PWR1.5 (GND), PWR1.6 (GND), PWR1.7 (GND), PWR1.8 (GND)
unnamed: D7.2 (A), L1.2
unnamed: D8.1 (K), L2.2

Notes on the sheet:
The bulk capacitance is tripled here because these ceramic caps derate to 3.54V with an 11.9V DC bias (-64.6%). Schottkys diodes have been substituted with a JLC Basic part.
Power circuit adapted from Paul Schreiber.
Note, in paults' schematic, the ferrite bead he uses is a Murata BLM21PG221SN1D which is 220R@100MHz. This part (120R@100MHz) is substituted because it's JLC Basic, but may not be as suitable a part.
+12V/-12V Rails
