colinbdclark/lichen-eurorack-hardware/Lichen_Design_Blocks.kicad_blocks/LDL1117 3.3V Regulator.kicad_block/LDL1117 3.3V Regulator.kicad_sch

## KiCad design Lichen_Design_Blocks.kicad_blocks/LDL1117 3.3V Regulator.kicad_block/LDL1117 3.3V Regulator.kicad_sch (2025-12-30)

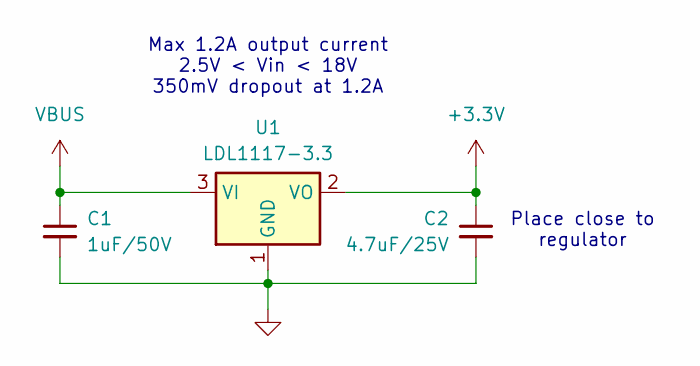
[picture p80: schematic LDL1117 3.3V Regulator.kicad_sch]

Parts:
C1: 1uF_0805_50V; C_0805; Part Number CL21B105KBFNNNE; LCSC C28323
C2: 4.7uF_0805_25V; C_0805; Part Number CL21A475KAQNNNE; LCSC C1779
U1: LDL1117-3.3; SOT-223-3_TabPin2; Part Number LDL1117S33R; LCSC C435835

Connections:
+3.3V: C2.1, U1.2 (VO)
GND: C1.2, C2.2, U1.1 (GND)
VBUS: C1.1, U1.3 (VI)

Notes on the sheet:
Max 1.2A output current 2.5V < Vin < 18V 350mV dropout at 1.2A
Place close to regulator
