colinbdclark/lichen-eurorack-hardware/Lichen_Design_Blocks.kicad_blocks/MIDI TRS Input Horizontal Jack LPZW Autocrossover.kicad_block/MIDI TRS Input Horizontal Jack LPZW Autocrossover.kicad_sch

## KiCad design Lichen_Design_Blocks.kicad_blocks/MIDI TRS Input Horizontal Jack LPZW Autocrossover.kicad_block/MIDI TRS Input Horizontal Jack LPZW Autocrossover.kicad_sch (2025-12-30)

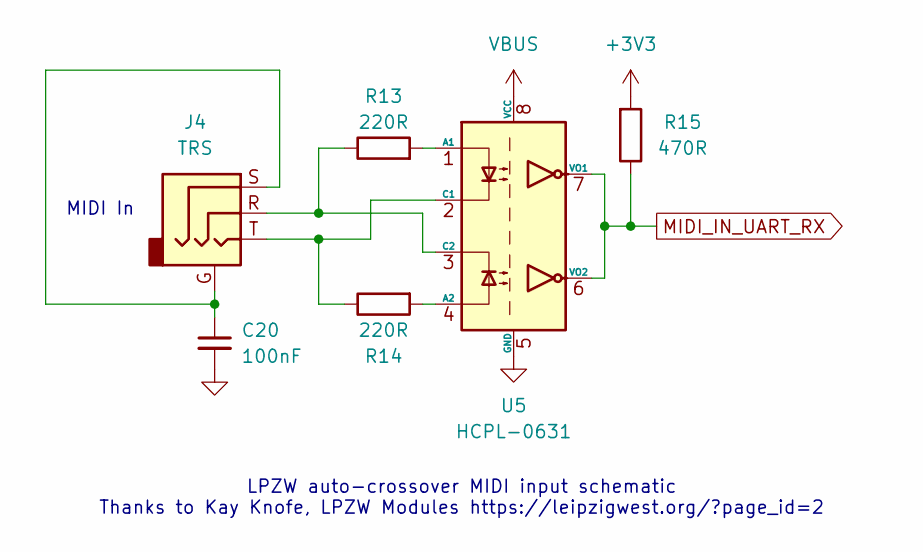
[picture p81: schematic MIDI TRS Input Horizontal Jack LPZW Autocrossover.kicad_sch]

Parts:
C20: 100nF_0402_16V; C_0402_1005Metric_small_pads; Part Number CL05B104KB54PNC; LCSC C307331
J4: TRS; Jack_3.5mm_KoreanHropartsElec_PJ-320D-4A_Horizontal_Overhan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; Part Number PJ-320D-4A; LCSC C95562
R13, R14: 220R_0402; R_0402_1005Metric; Part Number 0402WGF2200TCE; LCSC C25091
R15: 470R_0402; R_0402_1005Metric; Part Number 0402WGF4700TCE; LCSC C25117
U5: HCPL-0631; SOIC-8_3.9x4.9mm_P1.27mm; Part Number HCPL-0631-500E; LCSC C43949

Connections:
+3V3: R15.2
GND: C20.2, U5.5 (GND)
MIDI_IN_UART_RX: R15.1, U5.6 (VO2), U5.7 (VO1)
unnamed: C20.1, J4.G, J4.S
unnamed: J4.R, R13.1, U5.3 (C2)
unnamed: J4.T, R14.1, U5.2 (C1)
unnamed: R13.2, U5.1 (A1)
unnamed: R14.2, U5.4 (A2)
VBUS: U5.8 (VCC)

Notes on the sheet:
MIDI In
LPZW auto-crossover MIDI input schematic Thanks to Kay Knofe, LPZW Modules https://leipzigwest.org/?page_id=2
