colinbdclark/lichen-eurorack-hardware/Lichen_Design_Blocks.kicad_blocks/MIDI TRS Output Horizontal Jack.kicad_block/MIDI TRS Output Horizontal Jack.kicad_sch

## KiCad design Lichen_Design_Blocks.kicad_blocks/MIDI TRS Output Horizontal Jack.kicad_block/MIDI TRS Output Horizontal Jack.kicad_sch (2025-12-30)

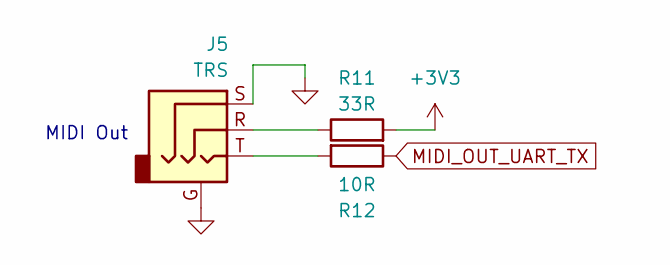
[picture p82: schematic MIDI TRS Output Horizontal Jack.kicad_sch]

Parts:
J5: TRS; Jack_3.5mm_KoreanHropartsElec_PJ-320D-4A_Horizontal_Overhan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; Part Number PJ-320D-4A; LCSC C95562
R11: 33R_0402; R_0402_1005Metric; Part Number 0402WGF330JTCE; LCSC C25105
R12: 10R_0402; R_0402_1005Metric; Part Number 0402WGF100JTCE; LCSC C25077

Connections:
+3V3: R11.2
GND: J5.G, J5.S
MIDI_OUT_UART_TX: R12.1
unnamed: J5.R, R11.1
unnamed: J5.T, R12.2

Notes on the sheet:
MIDI Out
