colinbdclark/lichen-eurorack-hardware/Lichen_Design_Blocks.kicad_blocks/RP2354A with Basic Components.kicad_block/RP2354A with Basic Components.kicad_sch

## KiCad design Lichen_Design_Blocks.kicad_blocks/RP2354A with Basic Components.kicad_block/RP2354A with Basic Components.kicad_sch (2026-03-04)

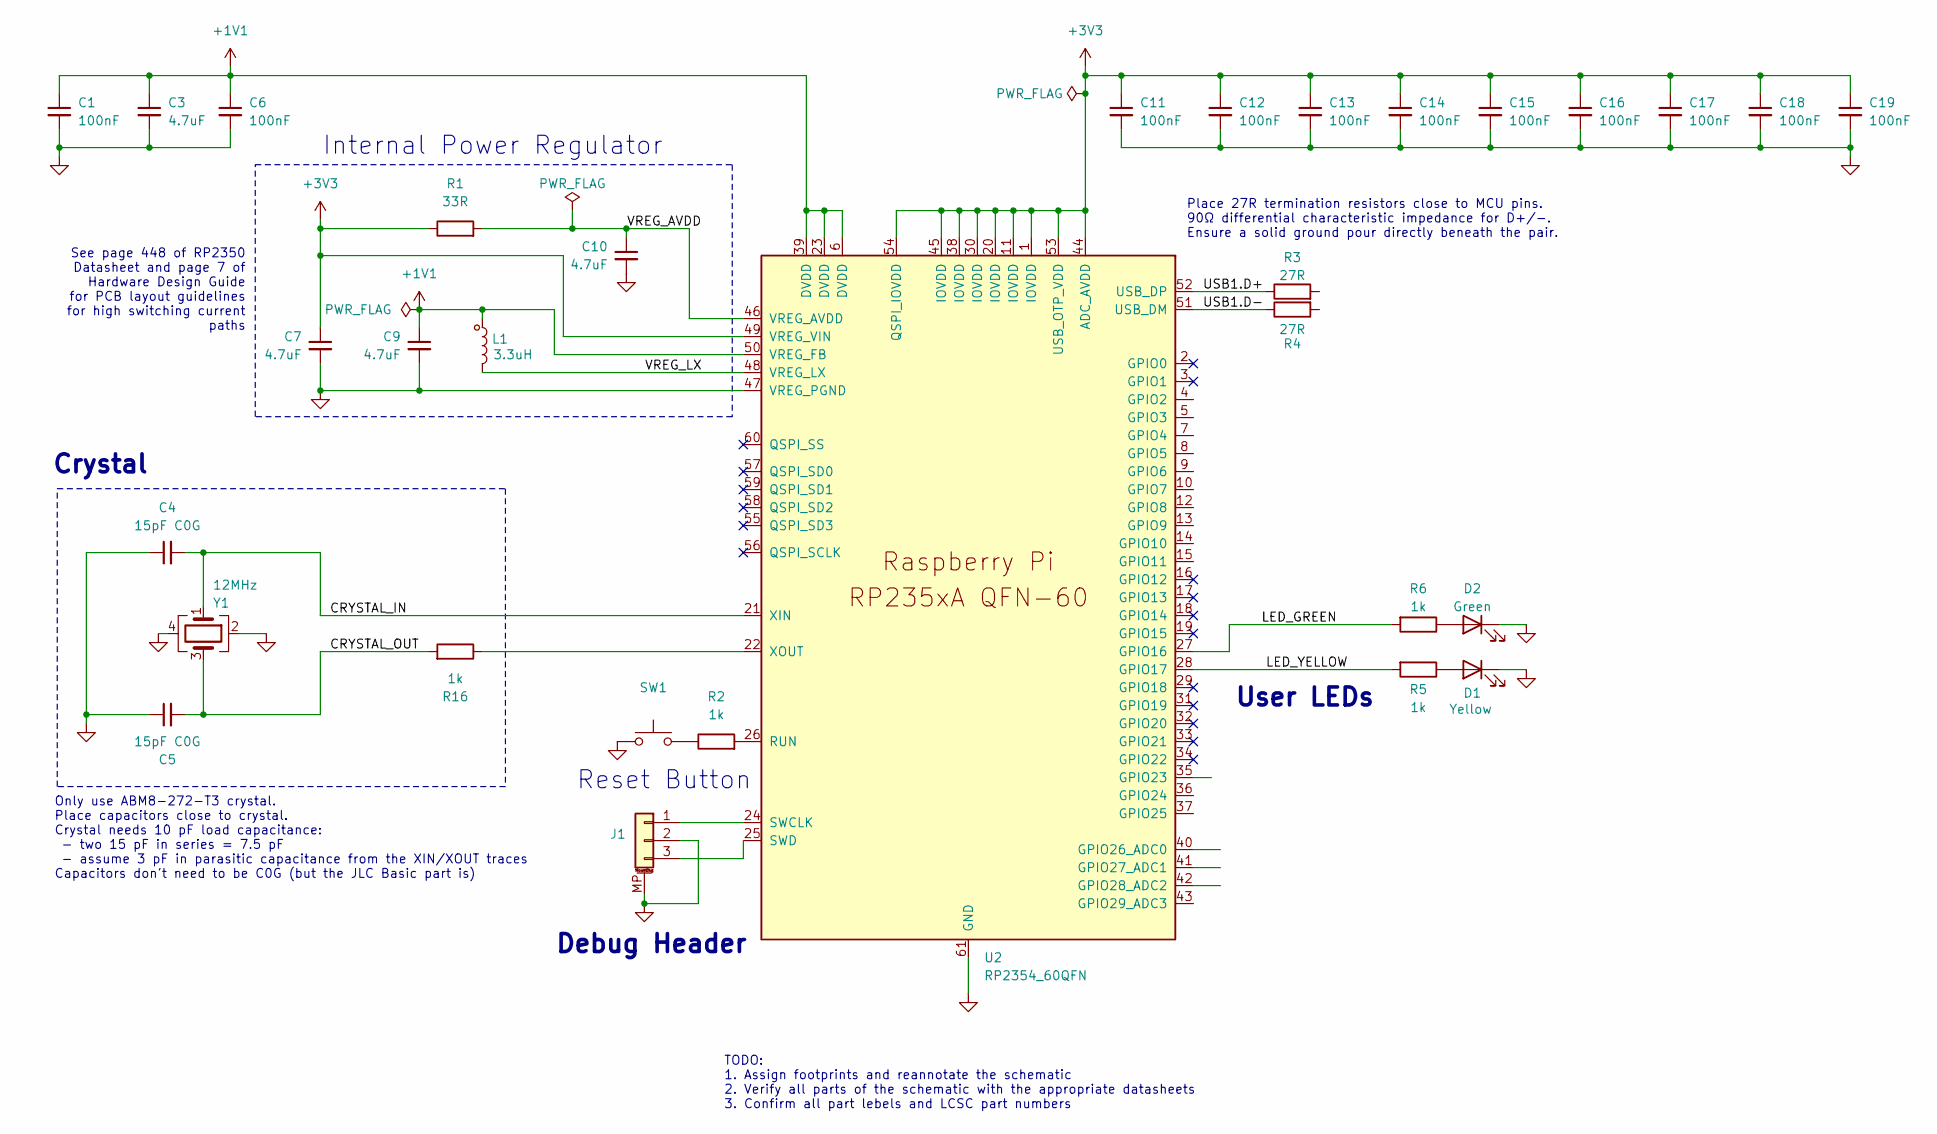
[picture p83: schematic RP2354A with Basic Components.kicad_sch]

Parts:
C1, C6, C11, C12, C13, C14, C15, C16, C17, C18, C19: 100nF; C_0402_1005Metric_small_pads; Part Number CL05B104KB54PNC; LCSC C307331
C3: 4.7uF; C_0402_1005Metric_small_pads; Part Number CL05A475MP5NRNC; LCSC C23733
C4, C5: 15pF; C_0402_1005Metric_small_pads; Part Number 0402CG150J500NT; LCSC C1548
C7, C9, C10: 4.7uF_0402; C_0402_1005Metric_small_pads; Part Number CL05A475MP5NRNC; LCSC C23733
D1: Yellow; LED_0805_2012Metric; Part Number KT-0805; LCSC C2296
D2: Green; LED_0805_2012Metric; Part Number KT-0805; LCSC C2296
J1: Conn_01x03_MountingPin; JST_SH_SM03B-SRSS-TB_1x03-1MP_P1.00mm_Horizontal; Part Number SM03B-SRSS-TB; LCSC C160403
L1: 3.3uH; L_pol_2016; Part Number AOTA-B201610S3R3-101-T; LCSC C42411119
R1: 33R_0402; R_0402_1005Metric; Part Number 0402WGF330JTCE; LCSC C25105
R2, R5, R6, R16: 1k_0402; R_0402_1005Metric; Part Number 0402WGF1001TCE; LCSC C11702
R3: 27R_0402; R_0402_1005Metric; Part Number 0402WGF270JTCE; LCSC C25100
R4: 33R_0402; R_0402_1005Metric; Part Number 0402WGF270JTCE; LCSC C25100
SW1: Button_Switch_SMD_Push_1P1T_Wurth; SW_Push_1P1T_NO_Vertical_Wuerth_434133025816; Part Number 434133025816; LCSC C5504987
U2: RP2354_60QFN; RP2350-QFN-60-1EP_7x7_P0.4mm_EP3.4x3.4mm_ThermalVias; Part Number RP2354A; LCSC C41378174
Y1: 12MHz; Crystal_SMD_3225-4Pin_3.2x2.5mm; Part Number ABM8-272-T3; LCSC C20625731

Connections:
+1V1: C1.1, C3.1, C6.1, C9.1, L1.1, U2.6 (DVDD), U2.23 (DVDD), U2.39 (DVDD), U2.50 (VREG_FB)
+3V3: C7.1, C11.1, C12.1, C13.1, C14.1, C15.1, C16.1, C17.1, C18.1, C19.1, R1.1, U2.1 (IOVDD), U2.11 (IOVDD), U2.20 (IOVDD), U2.30 (IOVDD), U2.38 (IOVDD), U2.44 (ADC_AVDD), U2.45 (IOVDD), U2.49 (VREG_VIN), U2.53 (USB_OTP_VDD), U2.54 (QSPI_IOVDD)
CRYSTAL_IN: C4.2, U2.21 (XIN), Y1.1
CRYSTAL_OUT: C5.2, R16.2, Y1.3
GND: C1.2, C3.2, C4.1, C5.1, C6.2, C7.2, C9.2, C10.2, C11.2, C12.2, C13.2, C14.2, C15.2, C16.2, C17.2, C18.2, C19.2, D1.1 (K), D2.1 (K), J1.2, J1.MP (MountPin), SW1.1, U2.47 (VREG_PGND), U2.61 (GND), Y1.2, Y1.4
LED_GREEN: R6.2, U2.27 (GPIO16)
LED_YELLOW: R5.2, U2.28 (GPIO17)
unnamed: D1.2 (A), R5.1
unnamed: D2.2 (A), R6.1
unnamed: J1.1, U2.24 (SWCLK)
unnamed: J1.3, U2.25 (SWD)
unnamed: R2.1, SW1.2
unnamed: R2.2, U2.26 (RUN)
unnamed: R16.1, U2.22 (XOUT)
USB1.D+: R3.1, U2.52 (USB_DP)
USB1.D-: R4.1, U2.51 (USB_DM)
VREG_AVDD: C10.1, R1.2, U2.46 (VREG_AVDD)
VREG_LX: L1.2, U2.48 (VREG_LX)

Notes on the sheet:
Place 27R termination resistors close to MCU pins. 90Ω differential characteristic impedance for D+/-. Ensure a solid ground pour directly beneath the pair.
TODO: 1. Assign footprints and reannotate the schematic 2. Verify all parts of the schematic with the appropriate datasheets 3. Confirm all part lebels and LCSC part numbers
Debug Header
Reset Button
See page 448 of RP2350 Datasheet and page 7 of Hardware Design Guide for PCB layout guidelines for high switching current paths
User LEDs
Internal Power Regulator
Crystal
Only use ABM8-272-T3 crystal. Place capacitors close to crystal. Crystal needs 10 pF load capacitance: - two 15 pF in series = 7.5 pF - assume 3 pF in parasitic capacitance from the XIN/XOUT traces Capacitors don't need to be C0G (but the JLC Basic part is)
