colinbdclark/lichen-eurorack-hardware/Lichen_Design_Blocks.kicad_blocks/Single Potetiometer Crossfader.kicad_block/Single Potetiometer Crossfader.kicad_sch

## KiCad design Lichen_Design_Blocks.kicad_blocks/Single Potetiometer Crossfader.kicad_block/Single Potetiometer Crossfader.kicad_sch (2025-12-17)

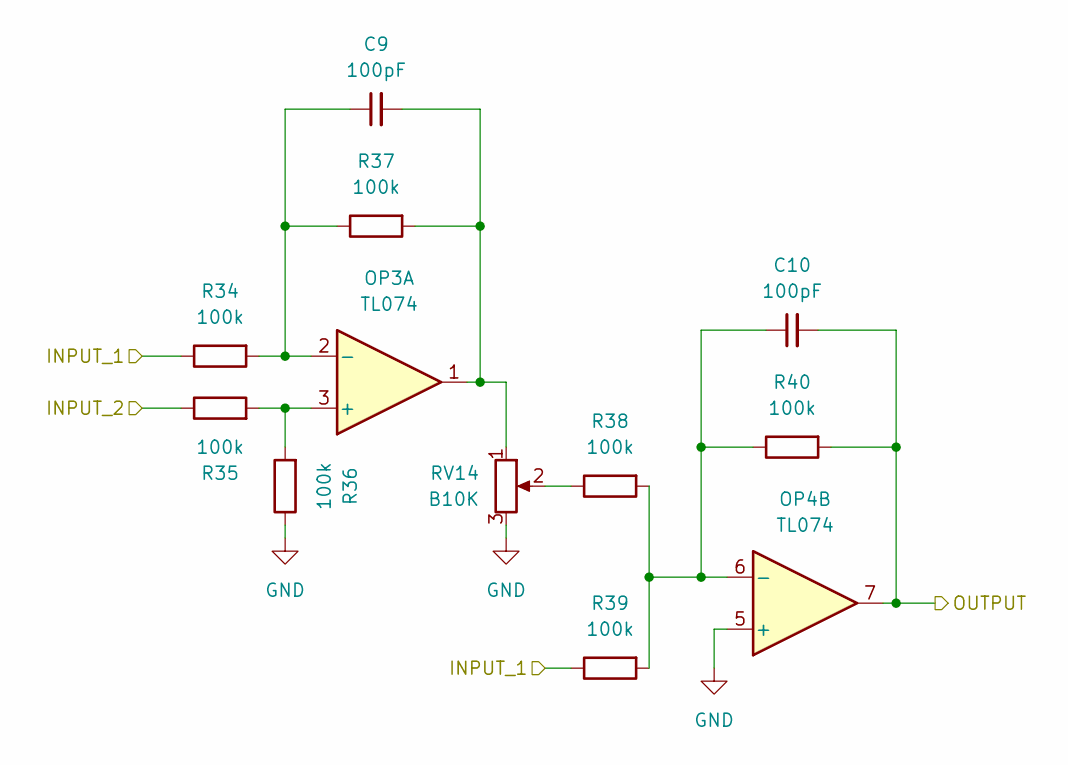
[picture p84: schematic Single Potetiometer Crossfader.kicad_sch]

Parts:
C9, C10: 100pF_C0G_0603_50V; C_0603; Part Number CC0603JRNPO9BN101; LCSC C14858
OP3: TL074; SOIC-14_3.9x8.65mm_Pitch1.27mm; Part Number TL074CDT; LCSC C6963
OP4: TL074
R34, R35, R36, R37, R38, R39, R40: 100k_0603; R_0603; Part Number 0603WAF1003T5E; JLCPCB ID C25803
RV14: B10K; Potentiometer_Alpha_RD901_Eurorack; Part Number RD901F-40

Connections:
GND: OP4.5 (+), R36.1, RV14.3
INPUT_1: R34.1, R39.1
INPUT_2: R35.1
unnamed: C9.1, OP3.2 (-), R34.2, R37.1
unnamed: C9.2, OP3.1, R37.2, RV14.1
unnamed: C10.1, OP4.6 (-), R38.2, R39.2, R40.1
unnamed: OP3.3 (+), R35.2, R36.2
unnamed: R38.1, RV14.2
OUTPUT: C10.2, OP4.7, R40.2
