colinbdclark/lichen-eurorack-hardware/Lichen_Design_Blocks.kicad_blocks/Stereo Moritz Klein Diode Ladder LPF.kicad_block/Stereo Moritz Klein Diode Ladder LPF.kicad_sch

## KiCad design Lichen_Design_Blocks.kicad_blocks/Stereo Moritz Klein Diode Ladder LPF.kicad_block/Stereo Moritz Klein Diode Ladder LPF.kicad_sch (2026-03-17)

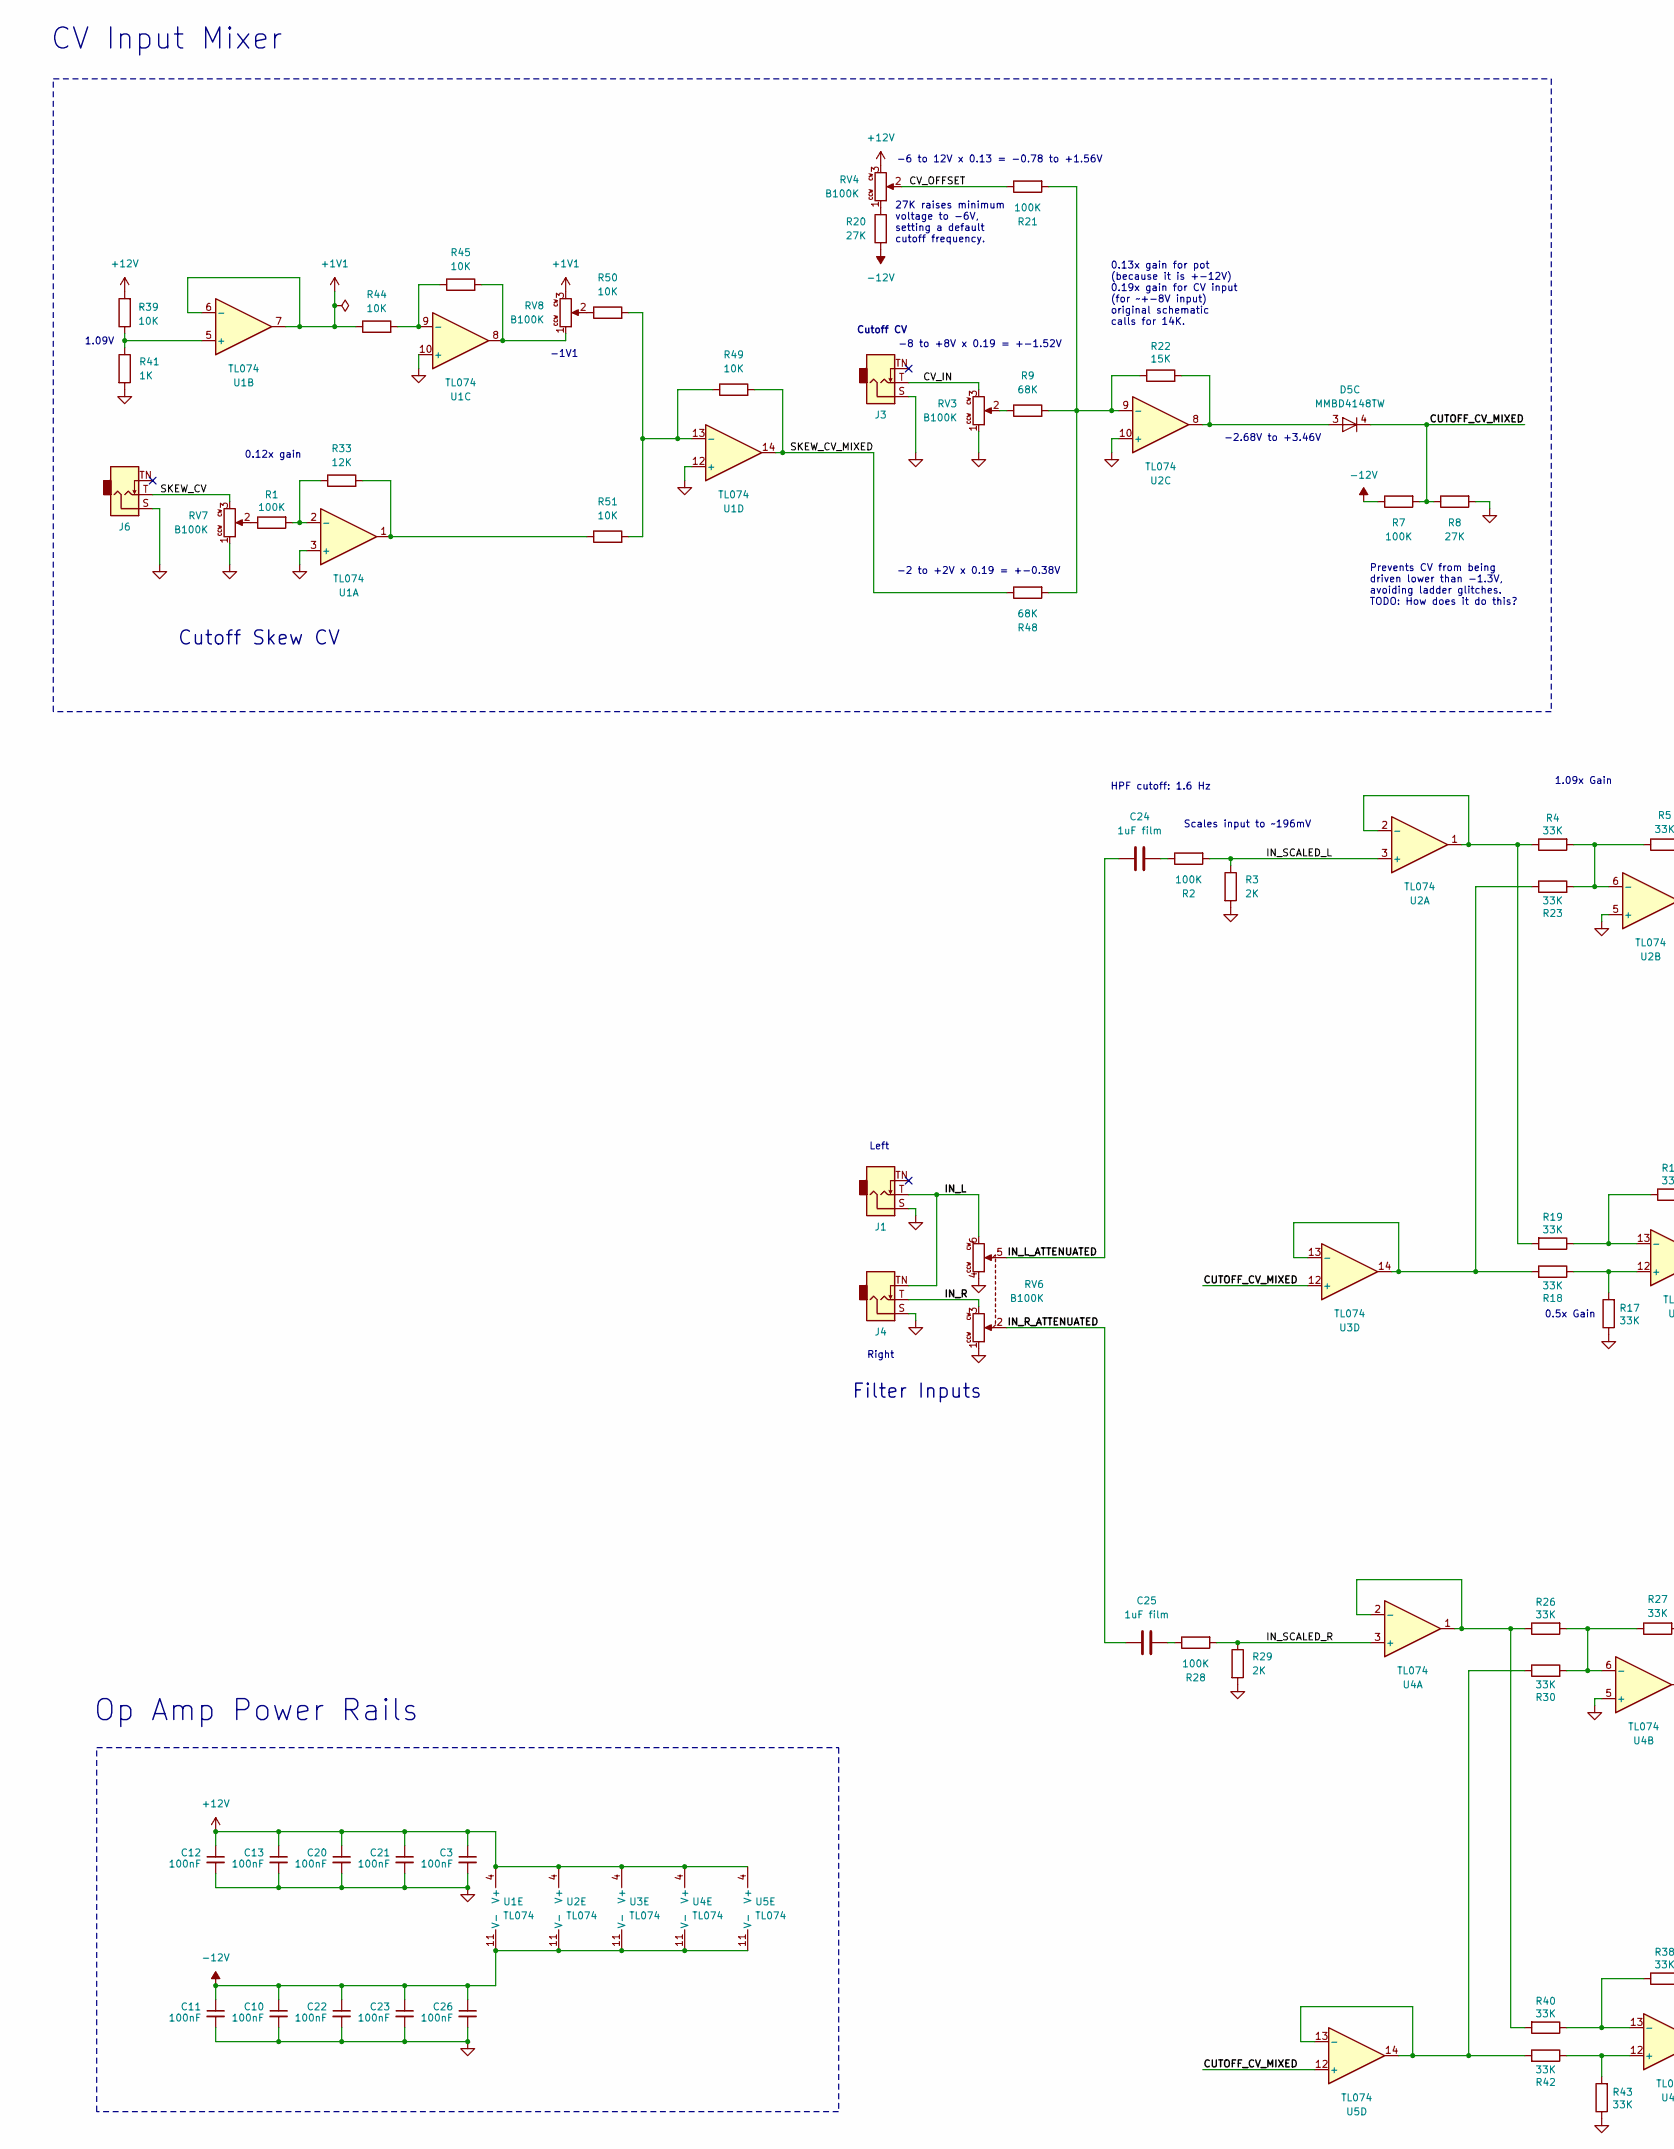
[picture p85: schematic Stereo Moritz Klein Diode Ladder LPF.kicad_sch, part in row 1, column 1]

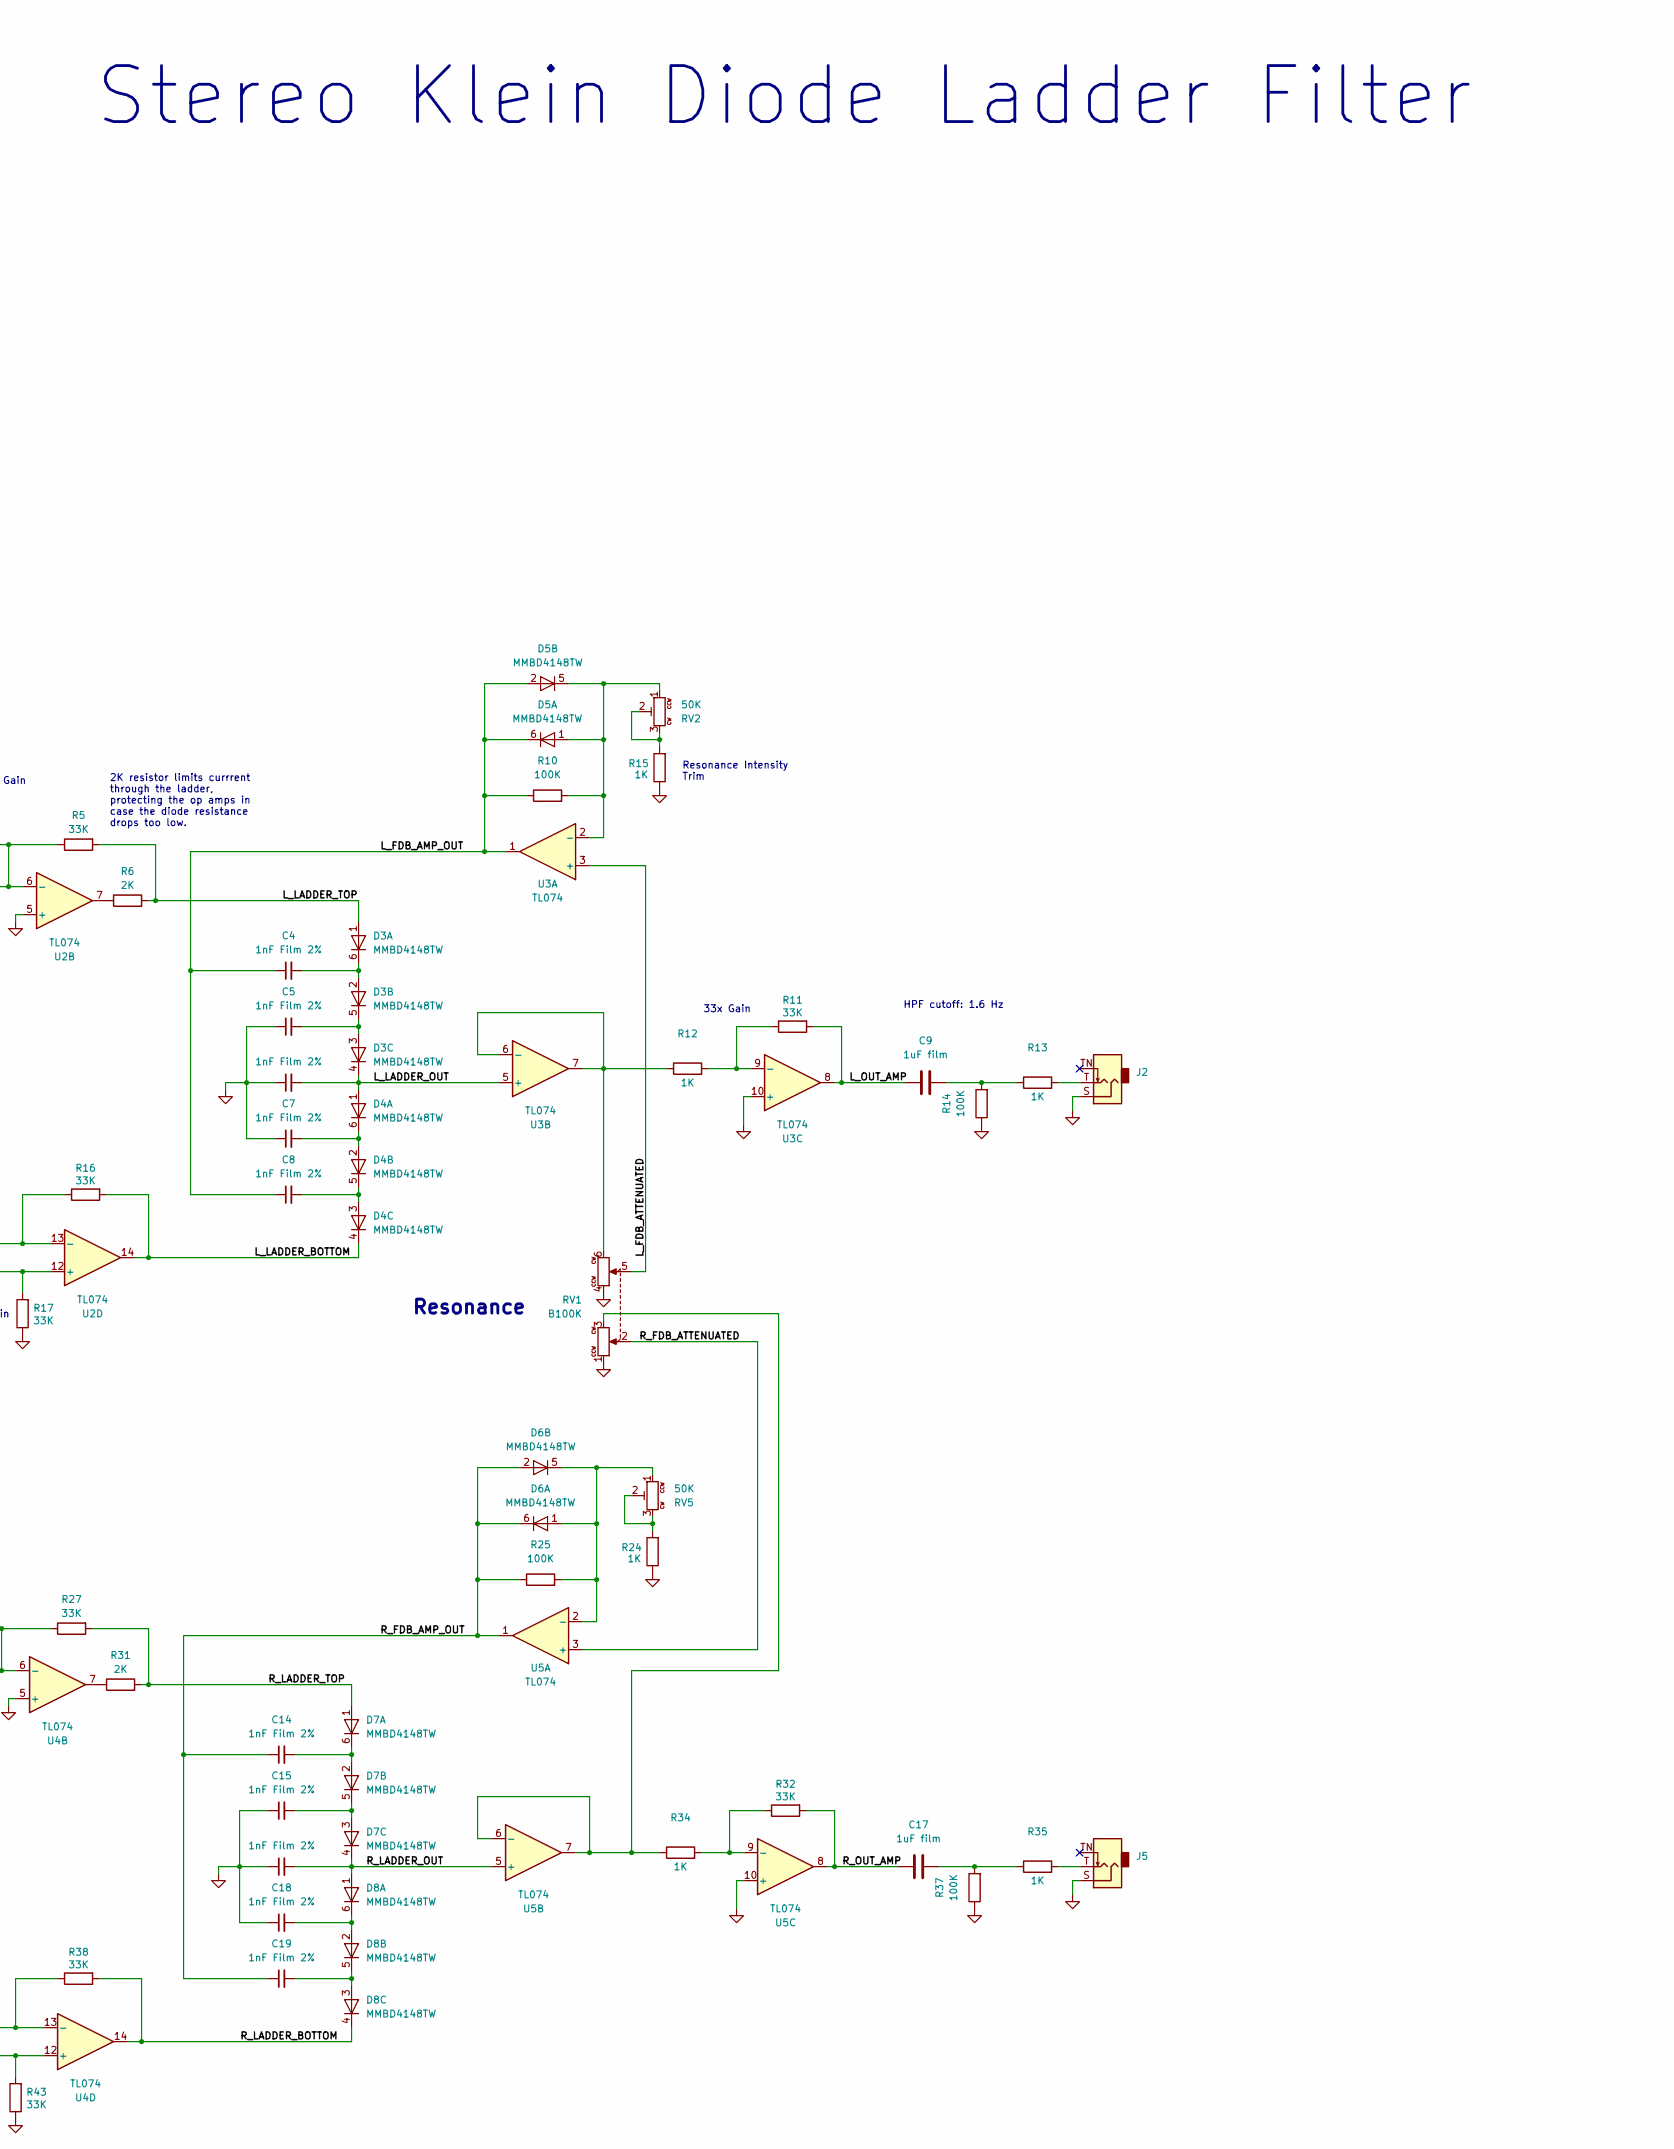
[picture p86: schematic Stereo Moritz Klein Diode Ladder LPF.kicad_sch, part in row 1, column 2]

Parts:
C3, C10, C11, C12, C13, C20, C21, C22, C23, C26: 100nF; C_0402_1005Metric_small_pads; Part Number CL05B104KB54PNC; LCSC C307331
C4, C5, C6, C7, C8, C14, C15, C16, C18, C19: 1nF; C_0805; Part Number ECHU1H102GX5; LCSC C569826
C9, C17, C24, C25: 1uF film; C_Rect_L7.2mm_W2.5mm_P5.00mm_FKS2_FKP2_MKS2_MKP2
D3, D4, D5, D6, D7, D8: MMBD4148TW; SOT-363_SC-70-6
J1, J2, J3, J4, J5, J6: Thonkiconn_Mono_Audio_Jack; Audio_Jack_Thonkiconn_Mono; Part Number WQP518MA/PJ398SM
R1, R2, R7, R10, R14, R21, R25, R28, R37: 100K; R_0603; Part Number 0603WAF1003T5E; LCSC C25803
R3, R6, R29, R31: 2K; R_0603; Part Number 0603WAF2001T5E; LCSC C22975
R4, R5, R11, R16, R17, R18, R19, R23, R26, R27, R30, R32, R38, R40, R42, R43: 33K; R_0603; Part Number 0603WAF3302T5E; LCSC C4216
R8, R20: 27K; R_0603; Part Number 0603WAF2702T5E; LCSC C22967
R9, R48: 68K; R_0603; Part Number 0603WAF6802T5E; LCSC C23231
R12, R13, R15, R24, R34, R35, R41: 1K; R_0603; Part Number 0603WAF1001T5E; LCSC C21190
R22: 15K; R_0603; Part Number 0603WAF1302T5E; JLCPCB ID C22797
R33: 12K; R_0603; Part Number 0603WAF1202T5E; JLCPCB ID C22790
R39, R44, R45, R49, R50, R51: 10K; R_0603; Part Number 0603WAF1002T5E; JLCPCB ID C25804
RV1, RV6: B100K; Potentiometer_Alpha_RD902F-40-00D_Dual_Vertical; Part Number RD90F-40
RV2, RV5: 50K; Potentiometer_Bourns_3224W_Vertical; Part Number 3224W-1-503E; LCSC C48484
RV3, RV4, RV7, RV8: B100K; Potentiometer_Alpha_RD901_Eurorack; Part Number RD901F-40
U1: TL074; SOIC-14_3.9x8.65mm_Pitch1.27mm; Part Number TL074IDR; LCSC C6964
U2, U3, U4, U5: TL074

Connections:
+1V1: R44.1, RV8.3, U1.6 (-), U1.7
+12V: C3.1, C12.1, C13.1, C20.1, C21.1, R39.2, RV4.3, U1.4 (V+), U2.4 (V+), U3.4 (V+), U4.4 (V+), U5.4 (V+)
-12V: C10.1, C11.1, C22.1, C23.1, C26.1, R7.1, R20.2, U1.11 (V-), U2.11 (V-), U3.11 (V-), U4.11 (V-), U5.11 (V-)
CUTOFF_CV_MIXED: D5.4 (K), R7.2, R8.1, U3.12 (+), U5.12 (+)
CV_IN: J3.T, RV3.3
CV_OFFSET: R21.1, RV4.2
GND: C3.2, C5.1, C6.1, C7.1, C10.2, C11.2, C12.2, C13.2, C15.1, C16.1, C18.1, C20.2, C21.2, C22.2, C23.2, C26.2, J1.S, J2.S, J3.S, J4.S, J5.S, J6.S, R3.2, R8.2, R14.1, R15.1, R17.1, R24.1, R29.2, R37.1, R41.2, R43.1, RV1.1, RV1.4, RV3.1, RV6.1, RV6.4, RV7.1, U1.3 (+), U1.10 (+), U1.12 (+), U2.5 (+), U2.10 (+), U3.10 (+), U4.5 (+), U5.10 (+)
IN_L: J1.T, J4.TN, RV6.6
IN_L_ATTENUATED: C24.1, RV6.5
IN_R: J4.T, RV6.3
IN_R_ATTENUATED: C25.1, RV6.2
IN_SCALED_L: R2.2, R3.1, U2.3 (+)
IN_SCALED_R: R28.2, R29.1, U4.3 (+)
L_FDB_AMP_OUT: C4.1, C8.1, D5.2 (A), D5.6 (K), R10.1, U3.1
L_FDB_ATTENUATED: RV1.5, U3.3 (+)
L_LADDER_BOTTOM: D4.4 (K), R16.2, U2.14
L_LADDER_OUT: C6.2, D3.4 (K), D4.1 (A), U3.5 (+)
L_LADDER_TOP: D3.1 (A), R5.2, R6.2
L_OUT_AMP: C9.1, R11.2, U3.8
unnamed: C4.2, D3.2 (A), D3.6 (K)
unnamed: C5.2, D3.3 (A), D3.5 (K)
unnamed: C7.2, D4.2 (A), D4.6 (K)
unnamed: C8.2, D4.3 (A), D4.5 (K)
unnamed: C9.2, R13.1, R14.2
unnamed: C14.2, D7.2 (A), D7.6 (K)
unnamed: C15.2, D7.3 (A), D7.5 (K)
unnamed: C17.2, R35.1, R37.2
unnamed: C18.2, D8.2 (A), D8.6 (K)
unnamed: C19.2, D8.3 (A), D8.5 (K)
unnamed: C24.2, R2.1
unnamed: C25.2, R28.1
unnamed: D5.1 (A), D5.5 (K), R10.2, RV2.1, U3.2 (-)
unnamed: D5.3 (A), R22.2, U2.8
unnamed: D6.1 (A), D6.5 (K), R25.2, RV5.1, U5.2 (-)
unnamed: J2.T, R13.2
unnamed: J5.T, R35.2
unnamed: R1.1, RV7.2
unnamed: R1.2, R33.1, U1.2 (-)
unnamed: R6.1, U2.7
unnamed: R9.1, RV3.2
unnamed: R11.1, R12.2, U3.9 (-)
unnamed: R12.1, RV1.6, U3.6 (-), U3.7
unnamed: R15.2, RV2.2, RV2.3
unnamed: R16.1, R19.1, U2.13 (-)
unnamed: R17.2, R18.1, U2.12 (+)
unnamed: R18.2, R23.1, U3.13 (-), U3.14
unnamed: R4.1, R19.2, U2.1, U2.2 (-)
unnamed: R20.1, RV4.1
unnamed: R9.2, R21.2, R22.1, R48.2, U2.9 (-)
unnamed: R4.2, R5.1, R23.2, U2.6 (-)
unnamed: R24.2, RV5.2, RV5.3
unnamed: R26.1, R40.2, U4.1, U4.2 (-)
unnamed: R26.2, R27.1, R30.2, U4.6 (-)
unnamed: R30.1, R42.2, U5.13 (-), U5.14
unnamed: R31.1, U4.7
unnamed: R32.1, R34.2, U5.9 (-)
unnamed: R33.2, R51.1, U1.1
unnamed: R34.1, RV1.3, U5.6 (-), U5.7
unnamed: R38.1, R40.1, U4.13 (-)
unnamed: R39.1, R41.1, U1.5 (+)
unnamed: R42.1, R43.2, U4.12 (+)
unnamed: R44.2, R45.1, U1.9 (-)
unnamed: R45.2, RV8.1, U1.8
unnamed: R49.1, R50.2, R51.2, U1.13 (-)
unnamed: R50.1, RV8.2
R_FDB_AMP_OUT: C14.1, C19.1, D6.2 (A), D6.6 (K), R25.1, U5.1
R_FDB_ATTENUATED: RV1.2, U5.3 (+)
R_LADDER_BOTTOM: D8.4 (K), R38.2, U4.14
R_LADDER_OUT: C16.2, D7.4 (K), D8.1 (A), U5.5 (+)
R_LADDER_TOP: D7.1 (A), R27.2, R31.2
R_OUT_AMP: C17.1, R32.2, U5.8
SKEW_CV: J6.T, RV7.3
SKEW_CV_MIXED: R48.1, R49.2, U1.14

Notes on the sheet:
-8 to +8V x 0.19 = +-1.52V
Left
HPF cutoff: 1.6 Hz
Right
Filter Inputs
0.12x gain
-2.68V to +3.46V
CV Input Mixer
Prevents CV from being driven lower than -1.3V, avoiding ladder glitches. TODO: How does it do this?
Cutoff CV
Op Amp Power Rails
Cutoff Skew CV
0.13x gain for pot (because it is +-12V) 0.19x gain for CV input (for ~+-8V input) original schematic calls for 14K.
Resonance Intensity Trim
0.5x Gain
1.09x Gain
27K raises minimum voltage to -6V, setting a default cutoff frequency.
33x Gain
1.09V
Scales input to ~196mV
Resonance
-2 to +2V x 0.19 = +-0.38V
-6 to 12V x 0.13 = -0.78 to +1.56V
Stereo Klein Diode Ladder Filter
-1V1
2K resistor limits currrent through the ladder, protecting the op amps in case the diode resistance drops too low.
