colinbdclark/lichen-eurorack-hardware/Lichen_Design_Blocks.kicad_blocks/TLV76733 5V to 3V3 Linear Regulator.kicad_block/TLV76733 5V to 3V3 Linear Regulator.kicad_sch

## KiCad design Lichen_Design_Blocks.kicad_blocks/TLV76733 5V to 3V3 Linear Regulator.kicad_block/TLV76733 5V to 3V3 Linear Regulator.kicad_sch (2026-03-04)

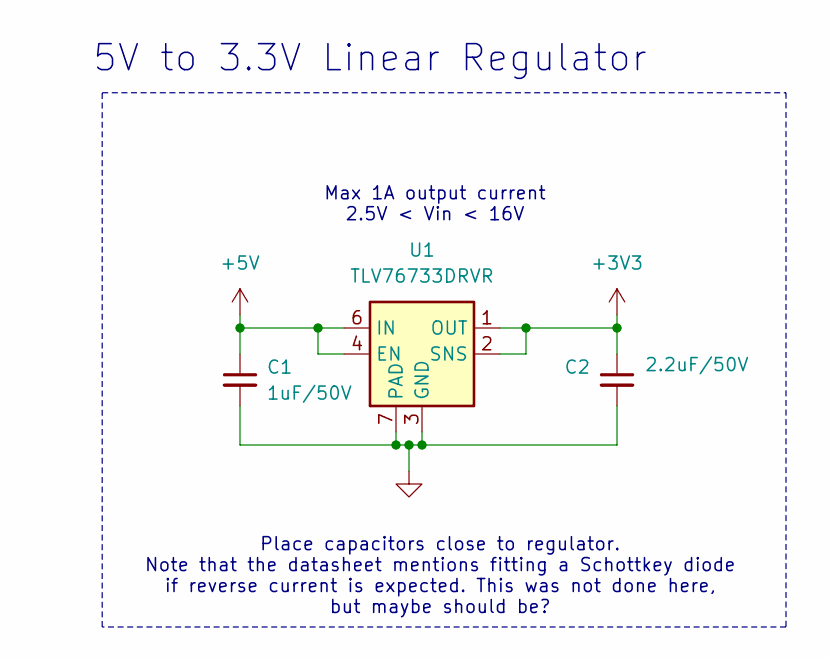
[picture p87: schematic TLV76733 5V to 3V3 Linear Regulator.kicad_sch]

Parts:
C1: 1uF; C_0805; Part Number CL21B105KBFNNNE; LCSC C28323
C2: 2.2uF; C_0805; Part Number CL21A225KBQNNNE; LCSC C377773
U1: TLV76733DRVR; WSON-6-1EP_2x2mm_P0.65mm_EP1x1.6mm_ThermalVias; Part Number TLV76733DRVR; LCSC C2848334

Connections:
+3V3: C2.1, U1.1 (OUT), U1.2 (SNS)
+5V: C1.1, U1.4 (EN), U1.6 (IN)
GND: C1.2, C2.2, U1.3 (GND), U1.5 (GND), U1.7 (PAD)

Notes on the sheet:
Max 1A output current 2.5V < Vin < 16V
5V to 3.3V Linear Regulator
Place capacitors close to regulator. Note that the datasheet mentions fitting a Schottkey diode if reverse current is expected. This was not done here, but maybe should be?
