colinbdclark/lichen-eurorack-hardware/Lichen_Design_Blocks.kicad_blocks/USB Connector with ESD Protection.kicad_block/USB Connector with ESD Protection.kicad_sch

## KiCad design Lichen_Design_Blocks.kicad_blocks/USB Connector with ESD Protection.kicad_block/USB Connector with ESD Protection.kicad_sch (2026-03-04)

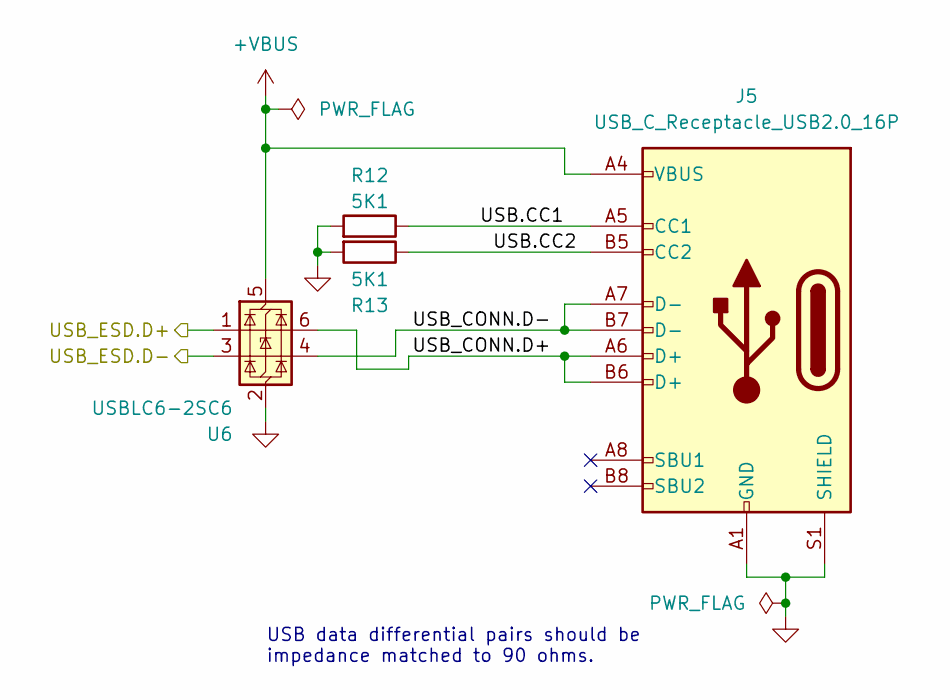
[picture p88: schematic USB Connector with ESD Protection.kicad_sch]

Parts:
J5: USB_C_Receptacle_USB2.0_16P; USB_C_Receptacle_HRO_TYPE-C-31-M-12_Overhanging; Part Number TYPE-C-31-M-12; LCSC C165948
R12, R13: 5.1K; R_0603; Part Number 0603WAF5101T5E; LCSC C23186
U6: USBLC6-2SC6; SOT-23-6; Part Number USBLC6-2SC6; LCSC C7519

Connections:
+VBUS: J5.A4 (VBUS), J5.A9 (VBUS), J5.B4 (VBUS), J5.B9 (VBUS), U6.5 (VBUS)
GND: J5.A1 (GND), J5.A12 (GND), J5.B1 (GND), J5.B12 (GND), J5.S1 (SHIELD), R12.2, R13.2, U6.2 (GND)
USB.CC1: J5.A5 (CC1), R12.1
USB.CC2: J5.B5 (CC2), R13.1
USB_CONN.D+: J5.A6 (D+), J5.B6 (D+), U6.6 (I/O1)
USB_CONN.D-: J5.A7 (D-), J5.B7 (D-), U6.4 (I/O2)
USB_ESD.D+: U6.1 (I/O1)
USB_ESD.D-: U6.3 (I/O2)

Notes on the sheet:
USB data differential pairs should be impedance matched to 90 ohms.
